crsjones/Southern-Cross-Computer-z80/SC-8x8_LED_Matrix/SC-8x8_R2/SC-8x8-R2.jpg

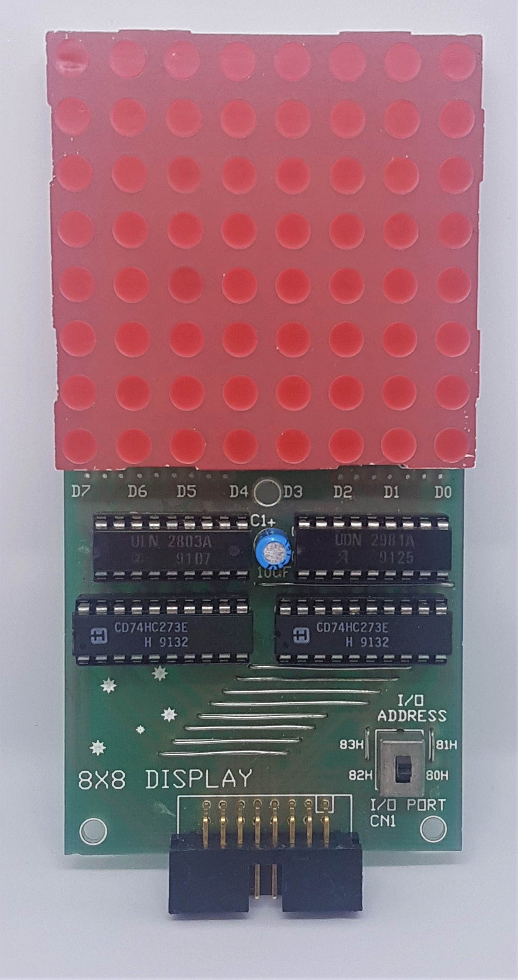
SC-8x8_LED_Matrix/SC-8x8_R2/SC-8x8-R2.jpg
