crsjones/Southern-Cross-Computer-z80/SC-8x8_LED_Matrix/SC-8x8_R4/Link.png

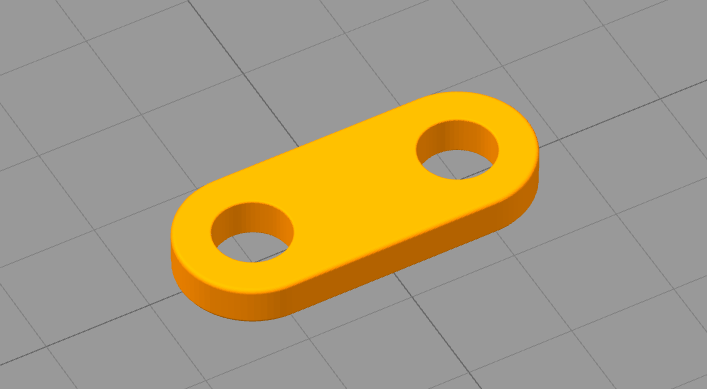
SC-8x8_LED_Matrix/SC-8x8_R4/Link.png
