crsjones/Southern-Cross-Computer-z80/SC-6850_Serial/SC-Serial_R1/SC-Serial_R1_PCB.jpg

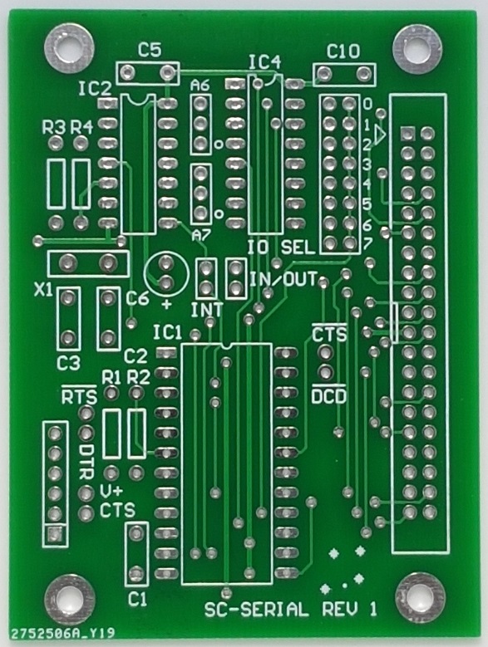
SC-6850_Serial/SC-Serial_R1/SC-Serial_R1_PCB.jpg
