crsjones/Southern-Cross-Computer-z80/SC-6850_Serial/SC-Serial_R2/SC-Serial_R2_PCB.jpg

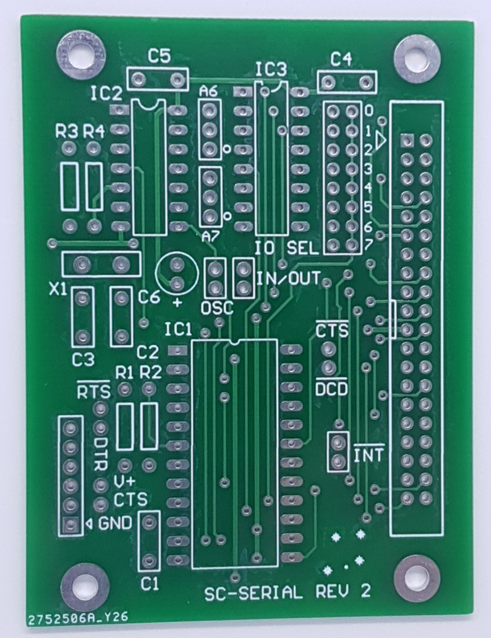
SC-6850_Serial/SC-Serial_R2/SC-Serial_R2_PCB.jpg
