crsjones/Southern-Cross-Computer-z80/SC-ALED/ALED10.png

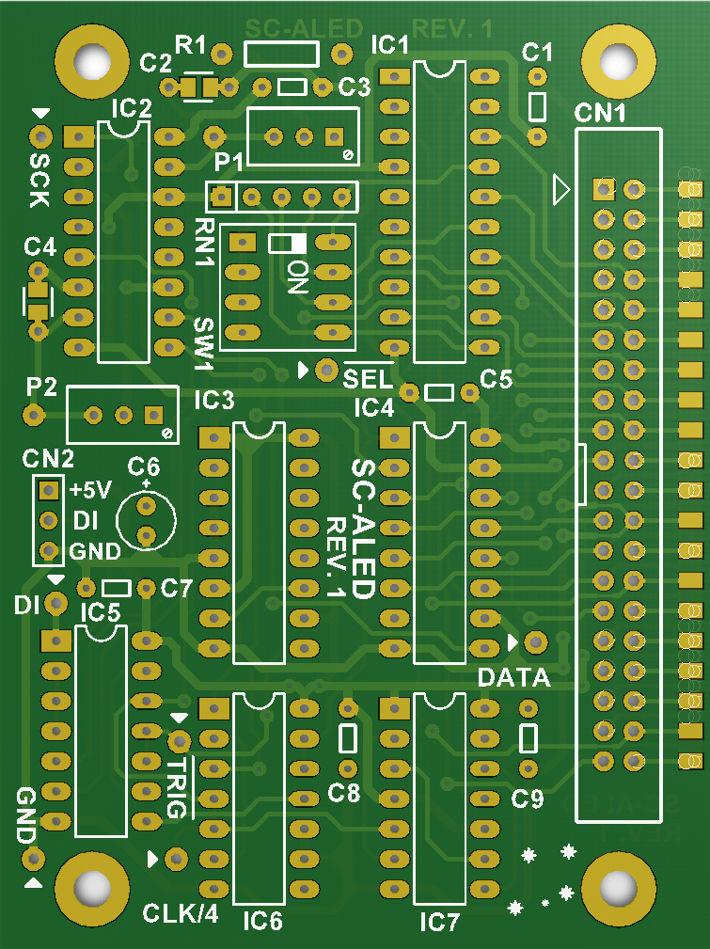
SC-ALED/ALED10.png
