crsjones/Southern-Cross-Computer-z80/SC-APU/SC-APU-R1/SC-APU-R1_PCB.jpg

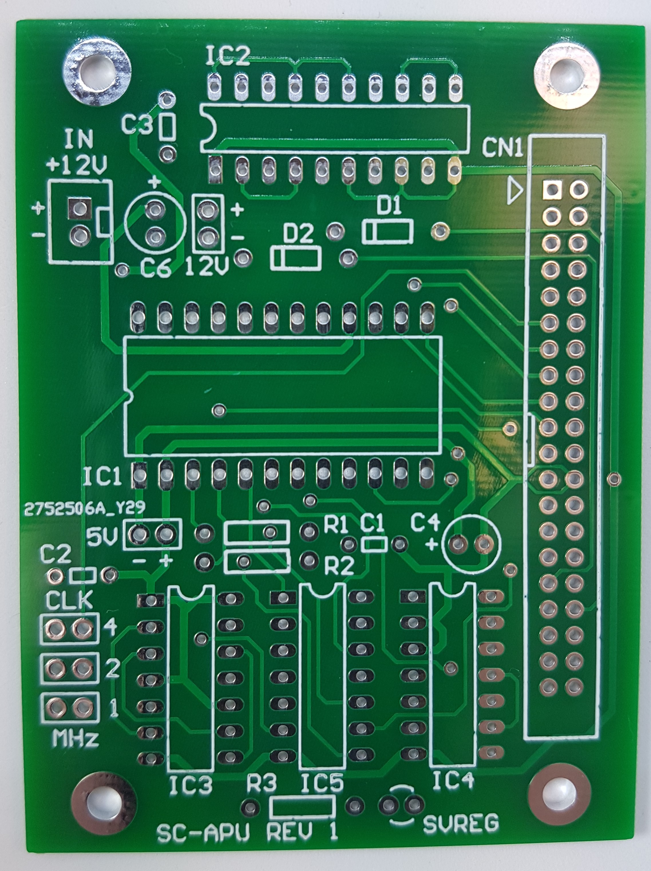
SC-APU/SC-APU-R1/SC-APU-R1_PCB.jpg
