crsjones/Southern-Cross-Computer-z80/SC-CF/SC-CFA-01_PCA.jpg

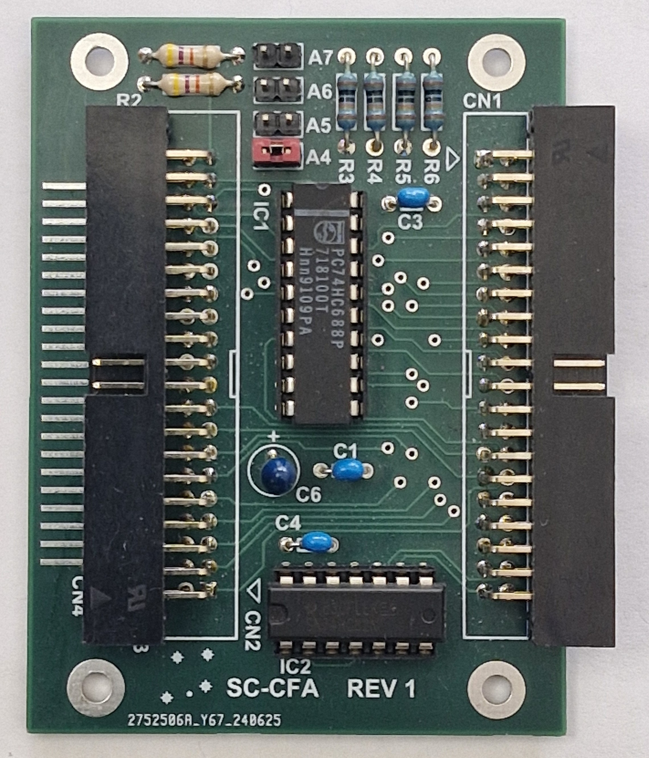
SC-CF/SC-CFA-01_PCA.jpg
