crsjones/Southern-Cross-Computer-z80/SC-CF/SC-CFA-02-PCB.png

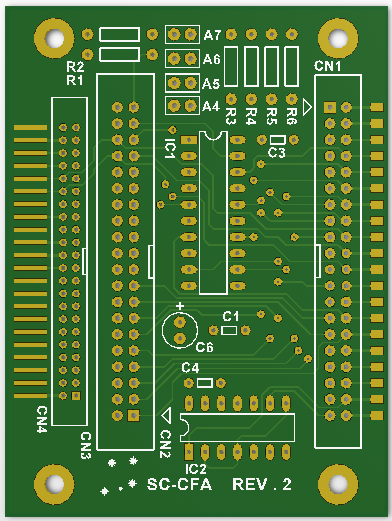
SC-CF/SC-CFA-02-PCB.png
