crsjones/Southern-Cross-Computer-z80/SC-CF/SC-CFA-FULL.jpg

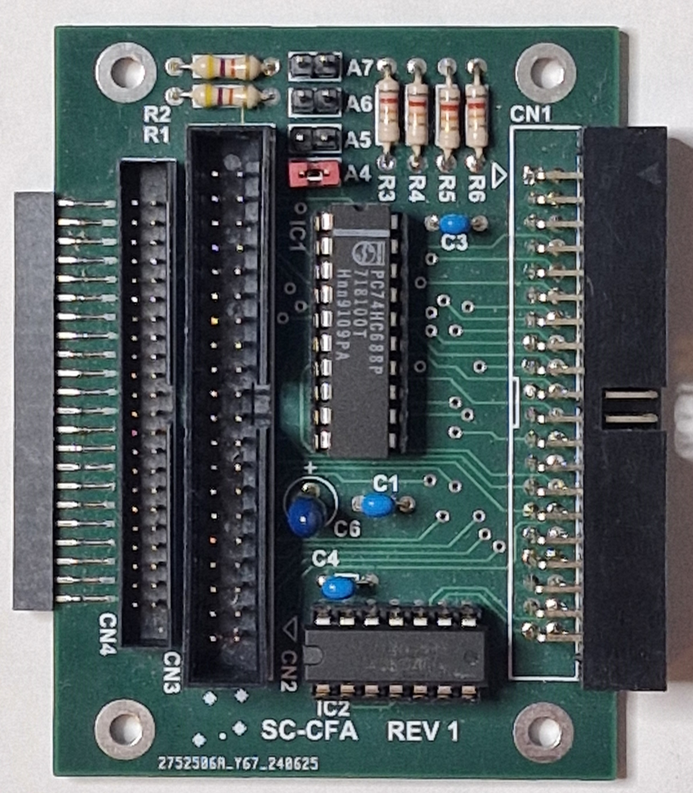
SC-CF/SC-CFA-FULL.jpg
