crsjones/Southern-Cross-Computer-z80/SC-CPU/Discrete Oscillator.jpg

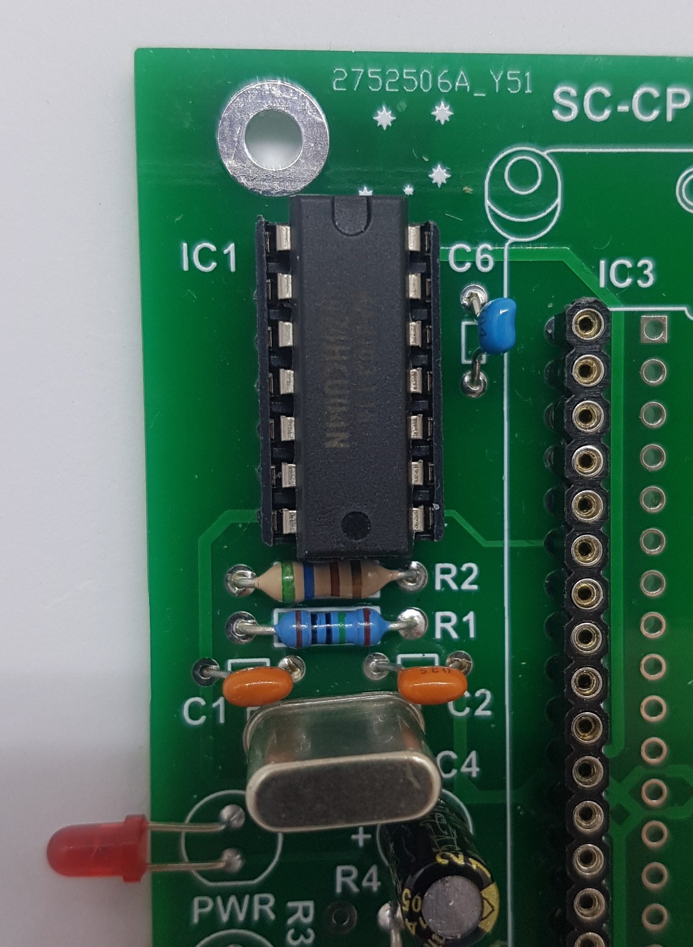
SC-CPU/Discrete Oscillator.jpg
