crsjones/Southern-Cross-Computer-z80/SC-CPU/SC-CPU-Blank.jpg

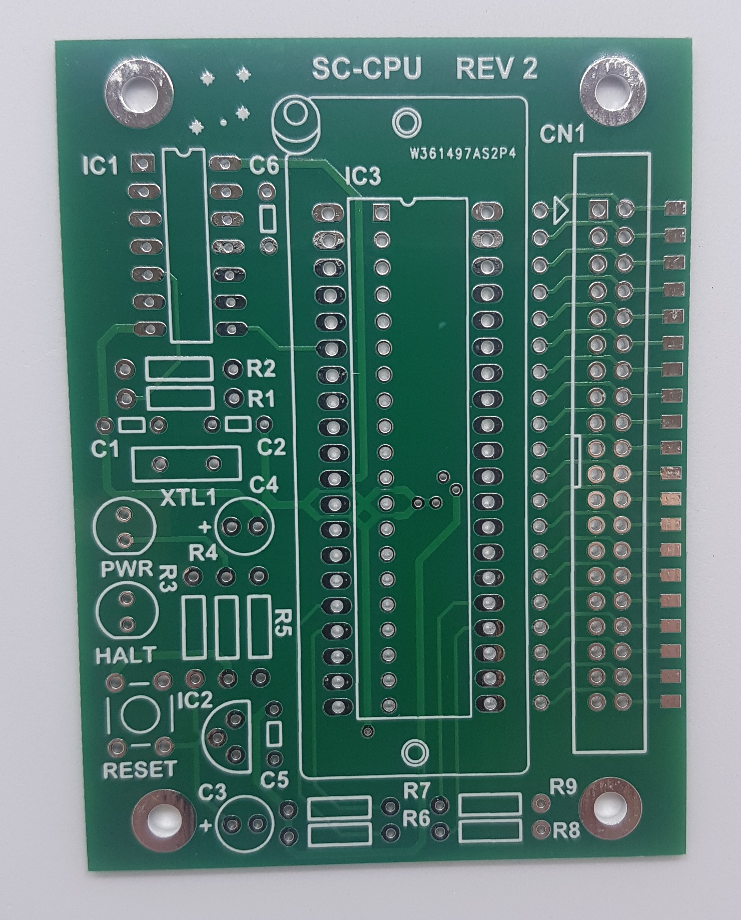
SC-CPU/SC-CPU-Blank.jpg
