crsjones/Southern-Cross-Computer-z80/SC-GBCART/SC-GBCART_R1.jpg

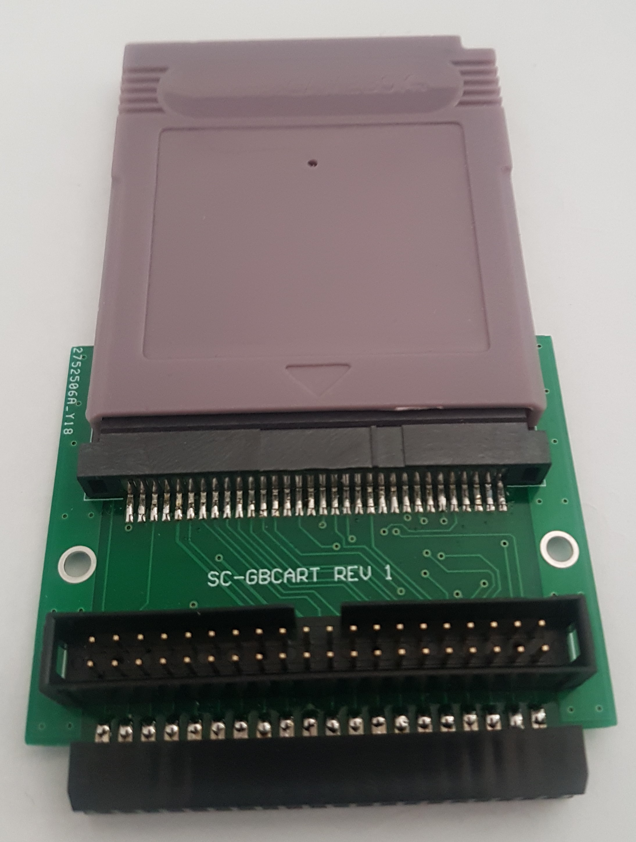
SC-GBCART/SC-GBCART_R1.jpg
