crsjones/Southern-Cross-Computer-z80/SouthernCrossSBC_PCB_R2/SC_R2.jpg

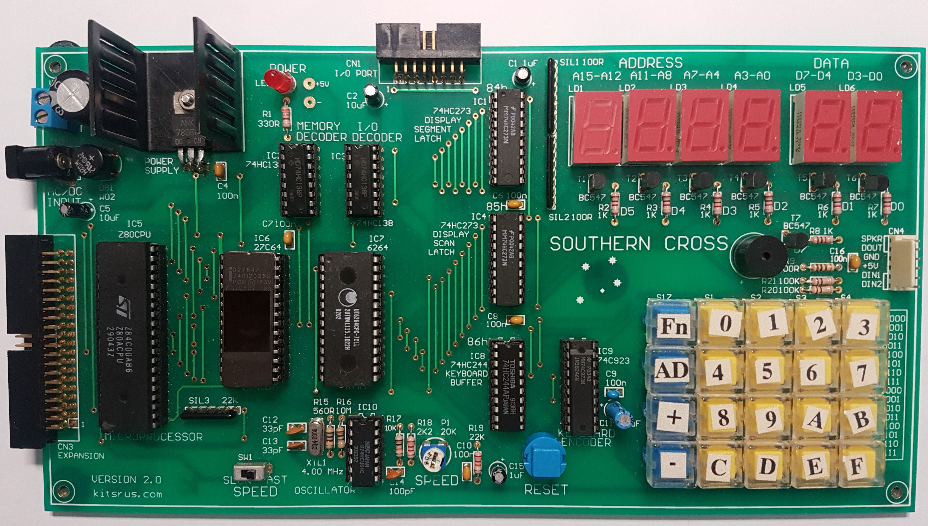
SouthernCrossSBC_PCB_R2/SC_R2.jpg
