crsjones/Southern-Cross-Computer-z80/SouthernCrossSBC_PCB_R3/SC30_Top.jpg

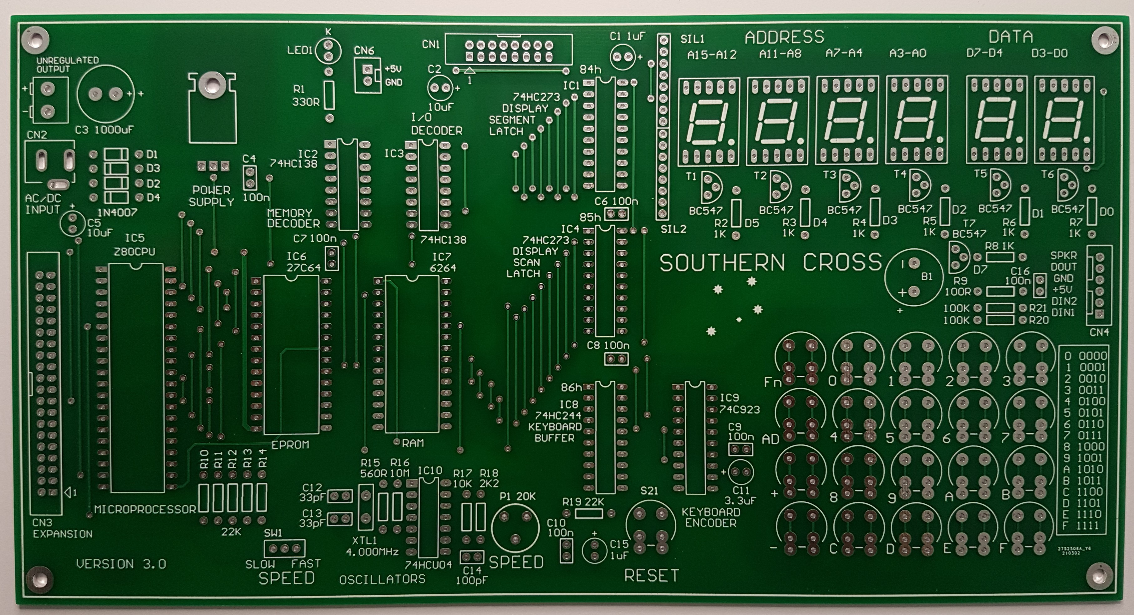
SouthernCrossSBC_PCB_R3/SC30_Top.jpg
