crsjones/Southern-Cross-Computer-z80/SouthernCrossSBC_PCB_R33/SC33-PCB-Bottom.jpg

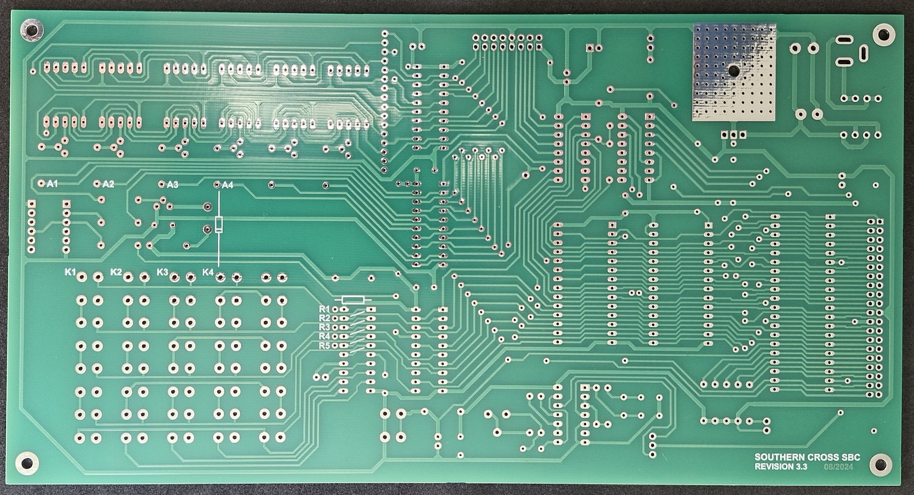
SouthernCrossSBC_PCB_R33/SC33-PCB-Bottom.jpg
