crsjones/Southern-Cross-Computer-z80/SouthernCrossSBC_PCB_R33/SC33-PCB-TOP.jpg

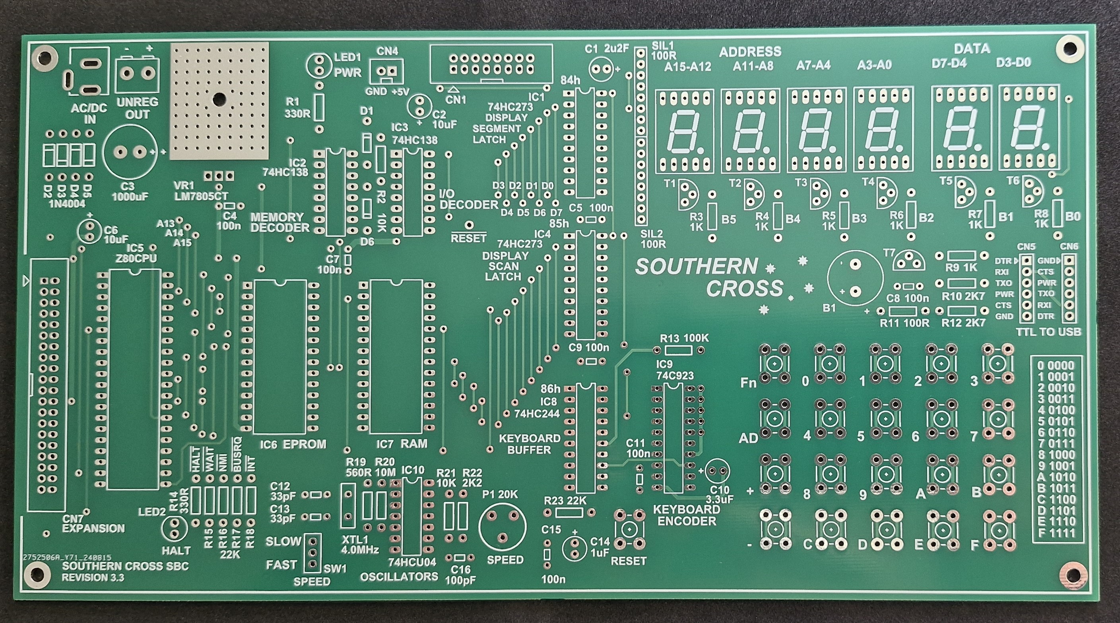
SouthernCrossSBC_PCB_R33/SC33-PCB-TOP.jpg
