crsjones/Southern-Cross-Computer-z80/SC-BP_Backplane/SC-BP-02/SC-BP-01ComponentOverlayandBOM.pdf

## SC-BP Expansion Backplane Rev. 1

## Component Overlay

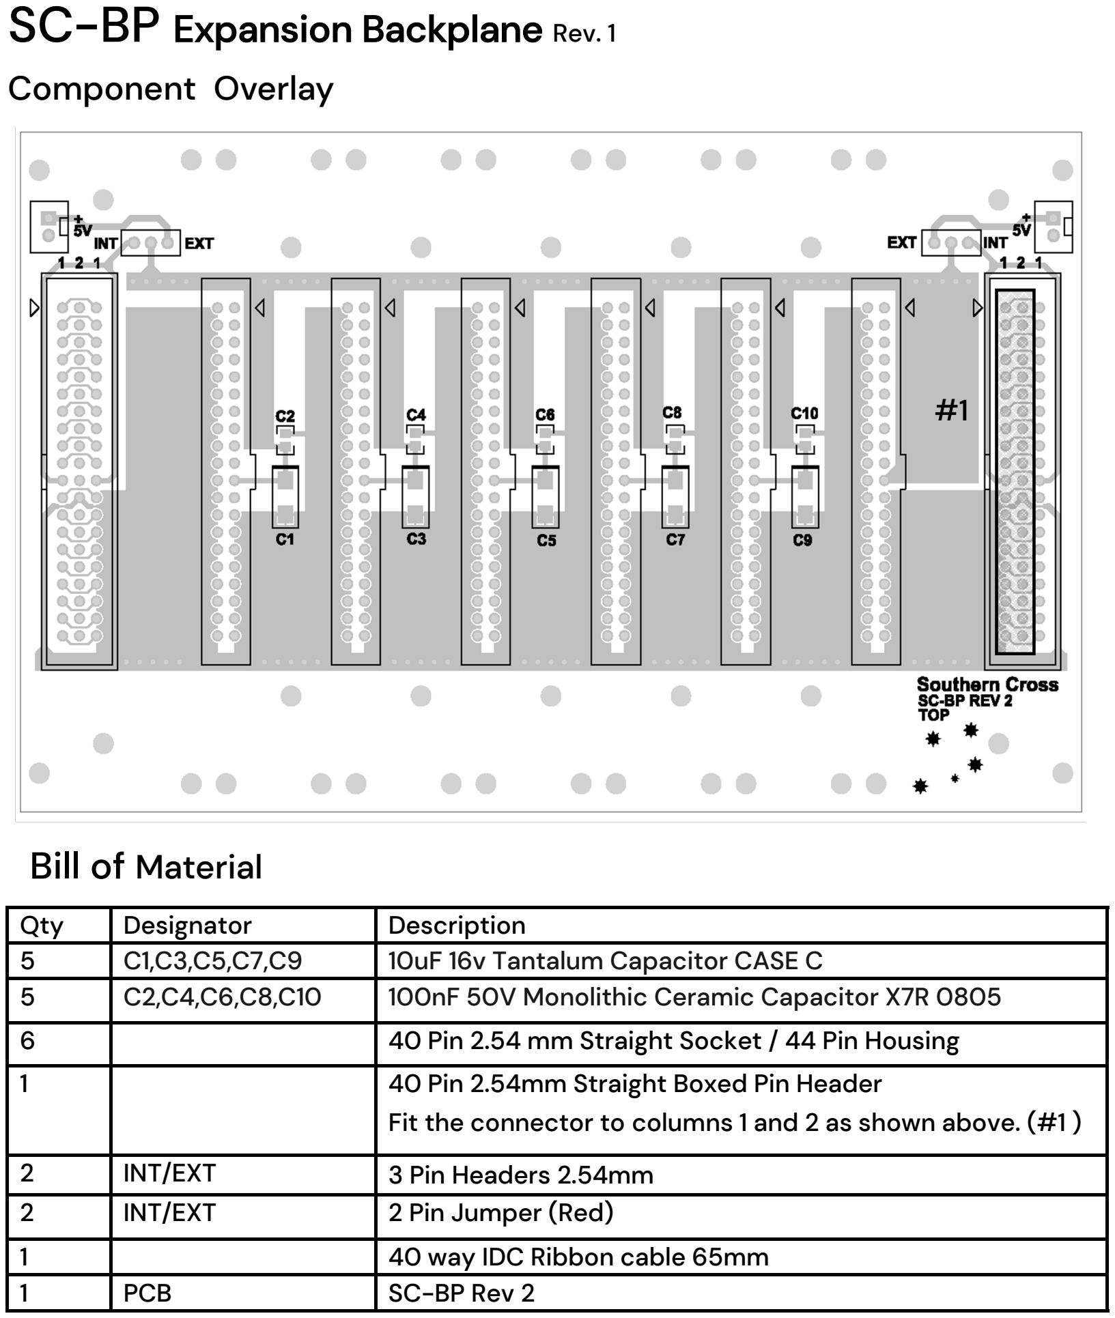
[picture p46: page 1]

## Bill of Material

Qty | Designator | Description
5 | C1,C3,C5,C7,C9 | 10uF 16v Tantalum Capacitor CASE C
5 | C2,C4,C6,C8,C10 | 100nF 50V Monolithic Ceramic Capacitor X7R 0805
6 40 Pin 2.54 mm Straight Socket / 44 Pin Housing
1 40 Pin 2.54mm Straight Boxed Pin Header | | Fit the connector to columns 1 and 2 as shown above. (#1 )
2 | INT/EXT | 3 Pin Headers 2.54mm
2 | INT/EXT | 2 Pin Jumper (Red)
1 40 way IDC Ribbon cable 65mm
1 | PCB | SC-BP Rev 2

#1
