crsjones/Southern-Cross-Computer-z80/SC-APU/SC-APU-R1/SC-APU-R1_Assembled.jpg

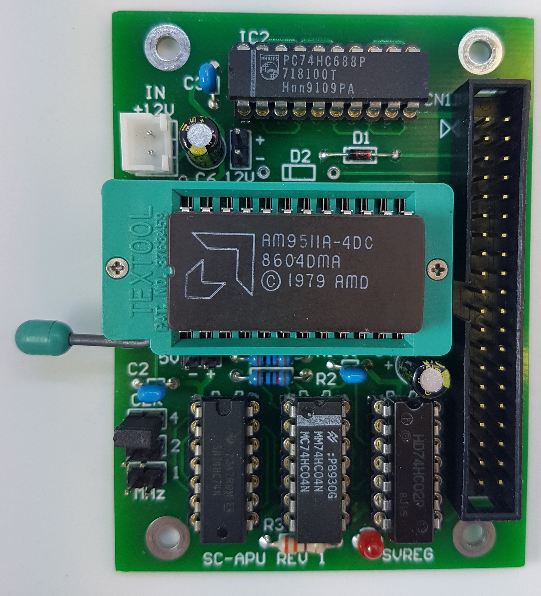
SC-APU/SC-APU-R1/SC-APU-R1_Assembled.jpg
