crsjones/Southern-Cross-Computer-z80/SC-APU/SC-APU-R2/SC-APU-R2_Assembled.jpg

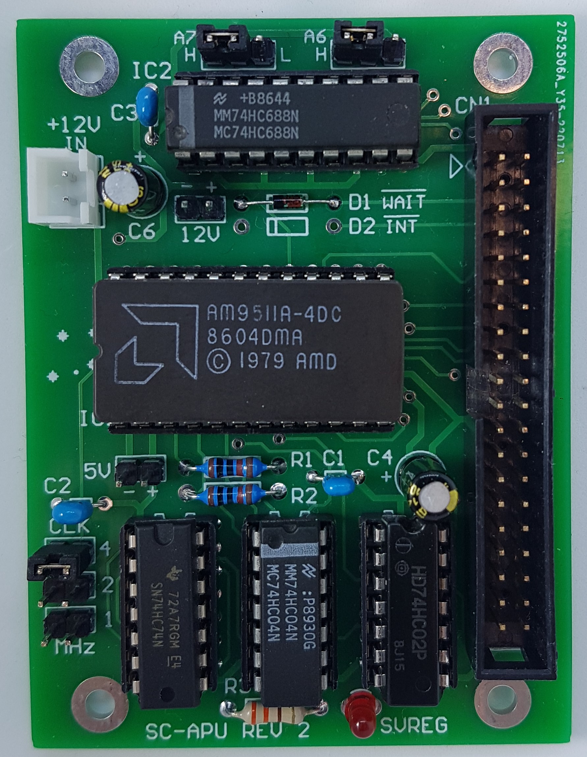
SC-APU/SC-APU-R2/SC-APU-R2_Assembled.jpg
