crsjones/Southern-Cross-Computer-z80/SC-CPU/SC-CPU-Assembled.jpg

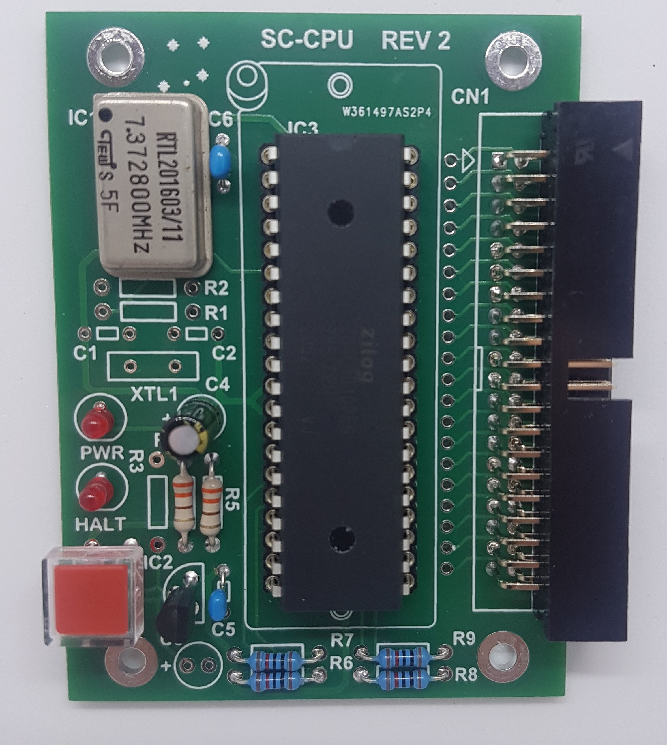
SC-CPU/SC-CPU-Assembled.jpg
