crsjones/Southern-Cross-Computer-z80/SC-MEM/SC-MEM-02-Assembled.jpg

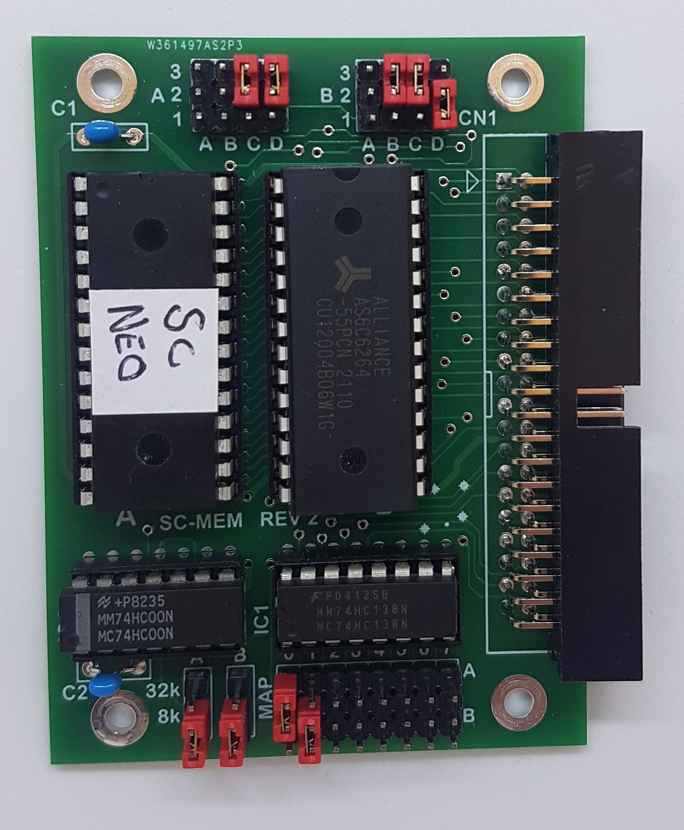
SC-MEM/SC-MEM-02-Assembled.jpg
