crsjones/Southern-Cross-Computer-z80/SouthernCrossSBC_PCB_R32/SC_R32-Assembled.jpg

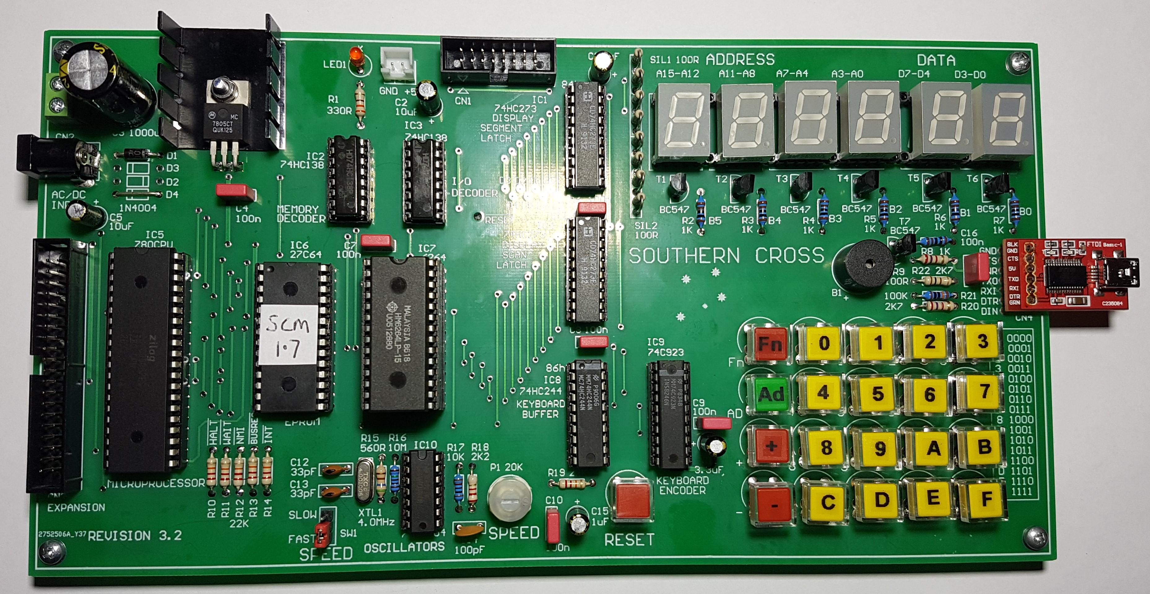
SouthernCrossSBC_PCB_R32/SC_R32-Assembled.jpg
