crsjones/Southern-Cross-Computer-z80/SC-8x8_LED_Matrix/SC-8x8_R4/SC-8X8_R5_Schematic.pdf

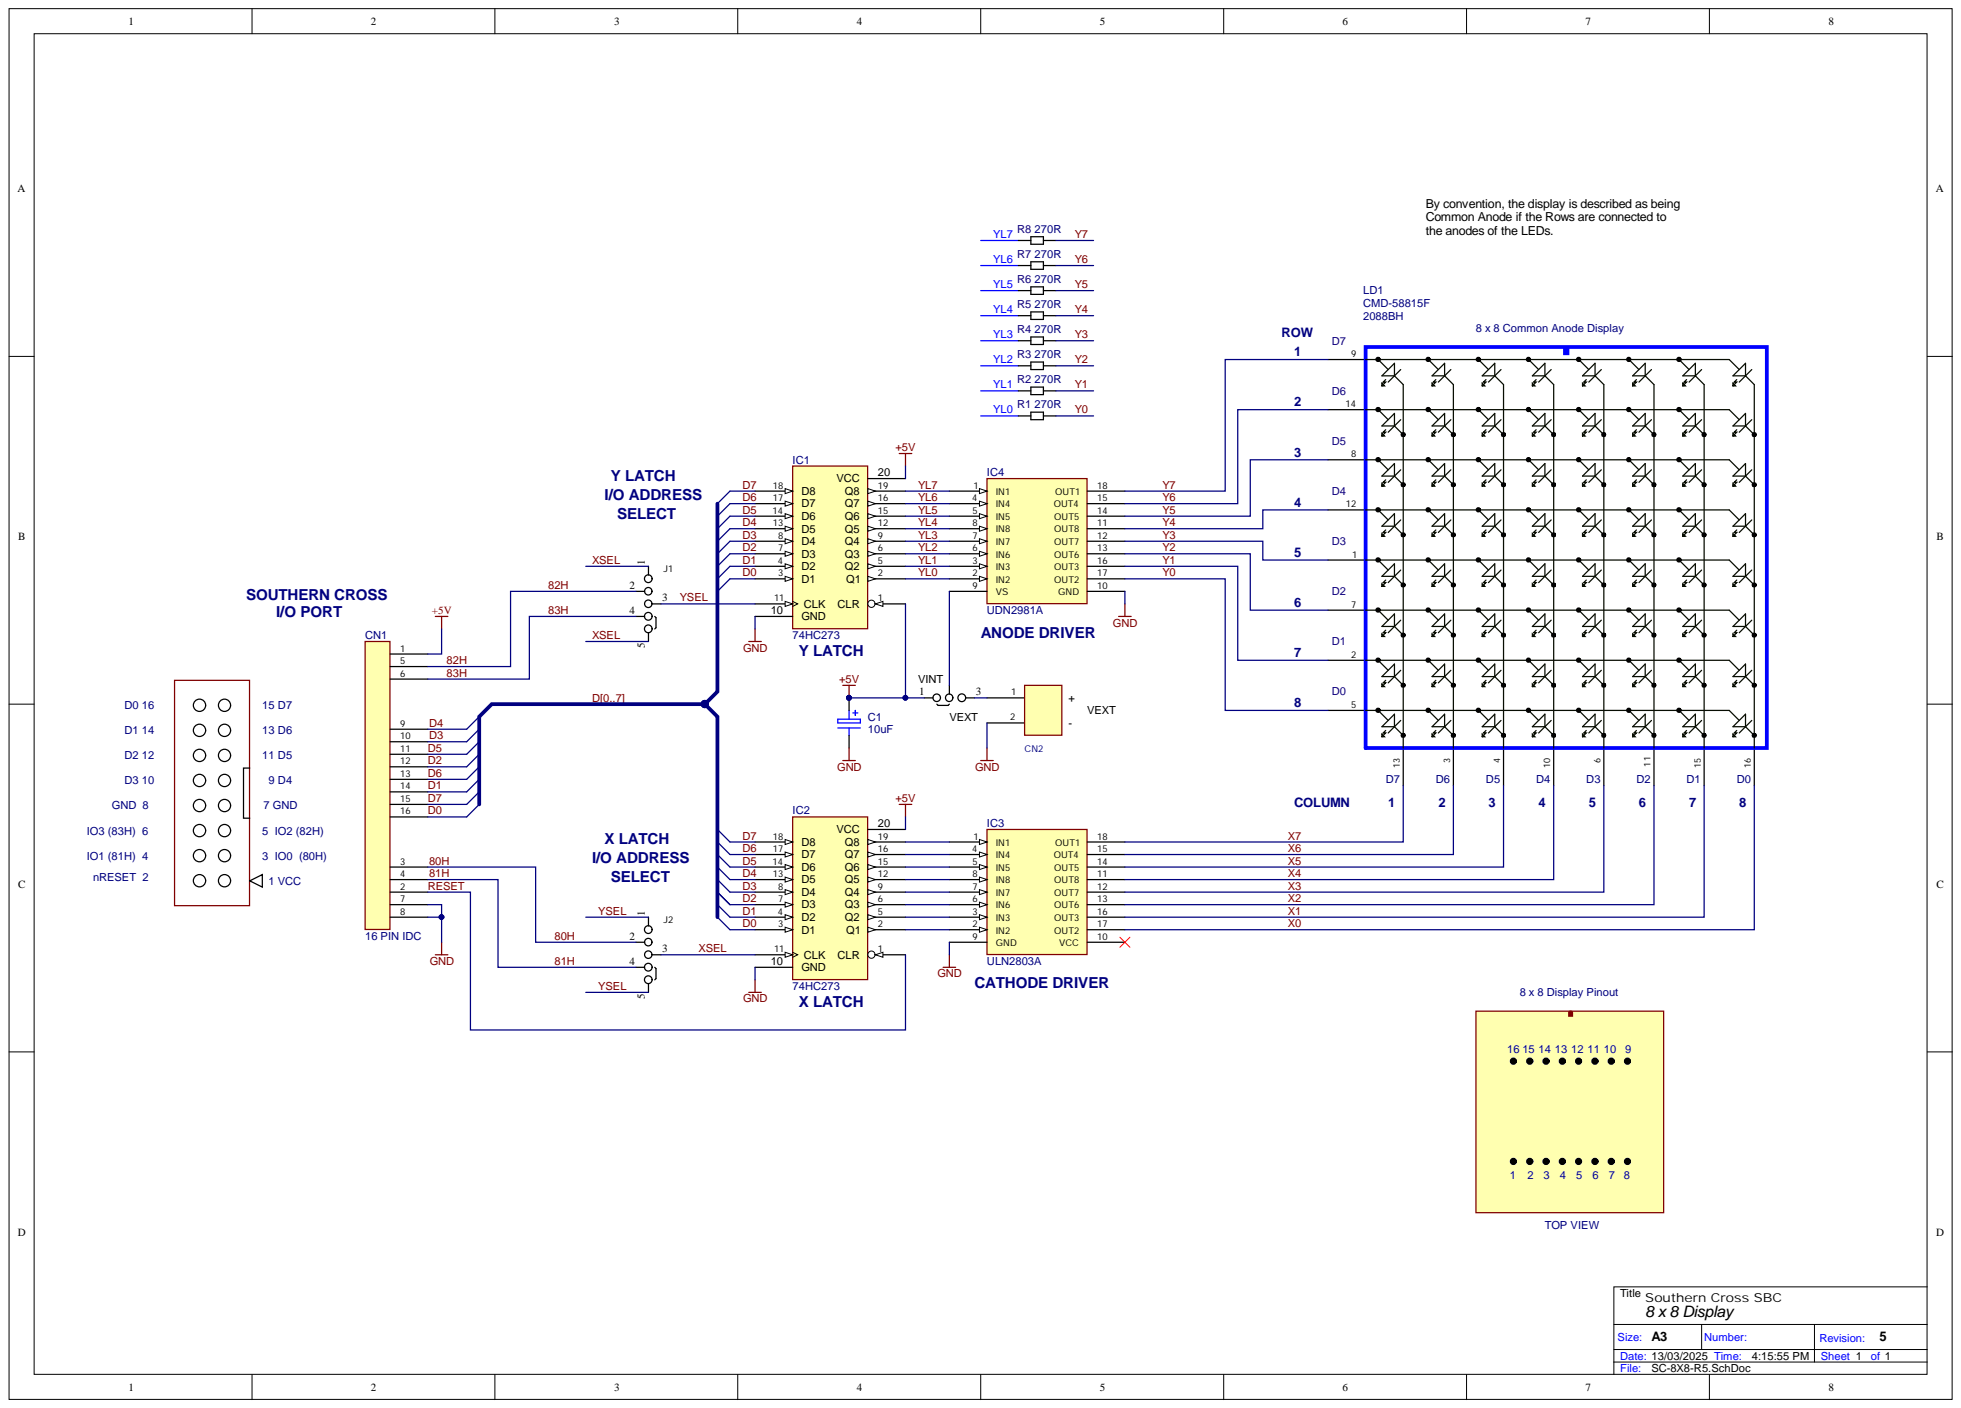
[picture p71: page 1]

8 | | Y 4
7 | Y 3
6 | | Y 2
3 | | Y 1

82H
83H

GND | 81H

Si ze: | Number: | Revis ion: 5
Date: 13/03/2025 T ime: 4:15:55 PM | | Sheet 1 of 1
