crsjones/Southern-Cross-Computer-z80/SC-8x8_LED_Matrix/SC-8x8_R3/SC-8X8-R3Schematic.pdf

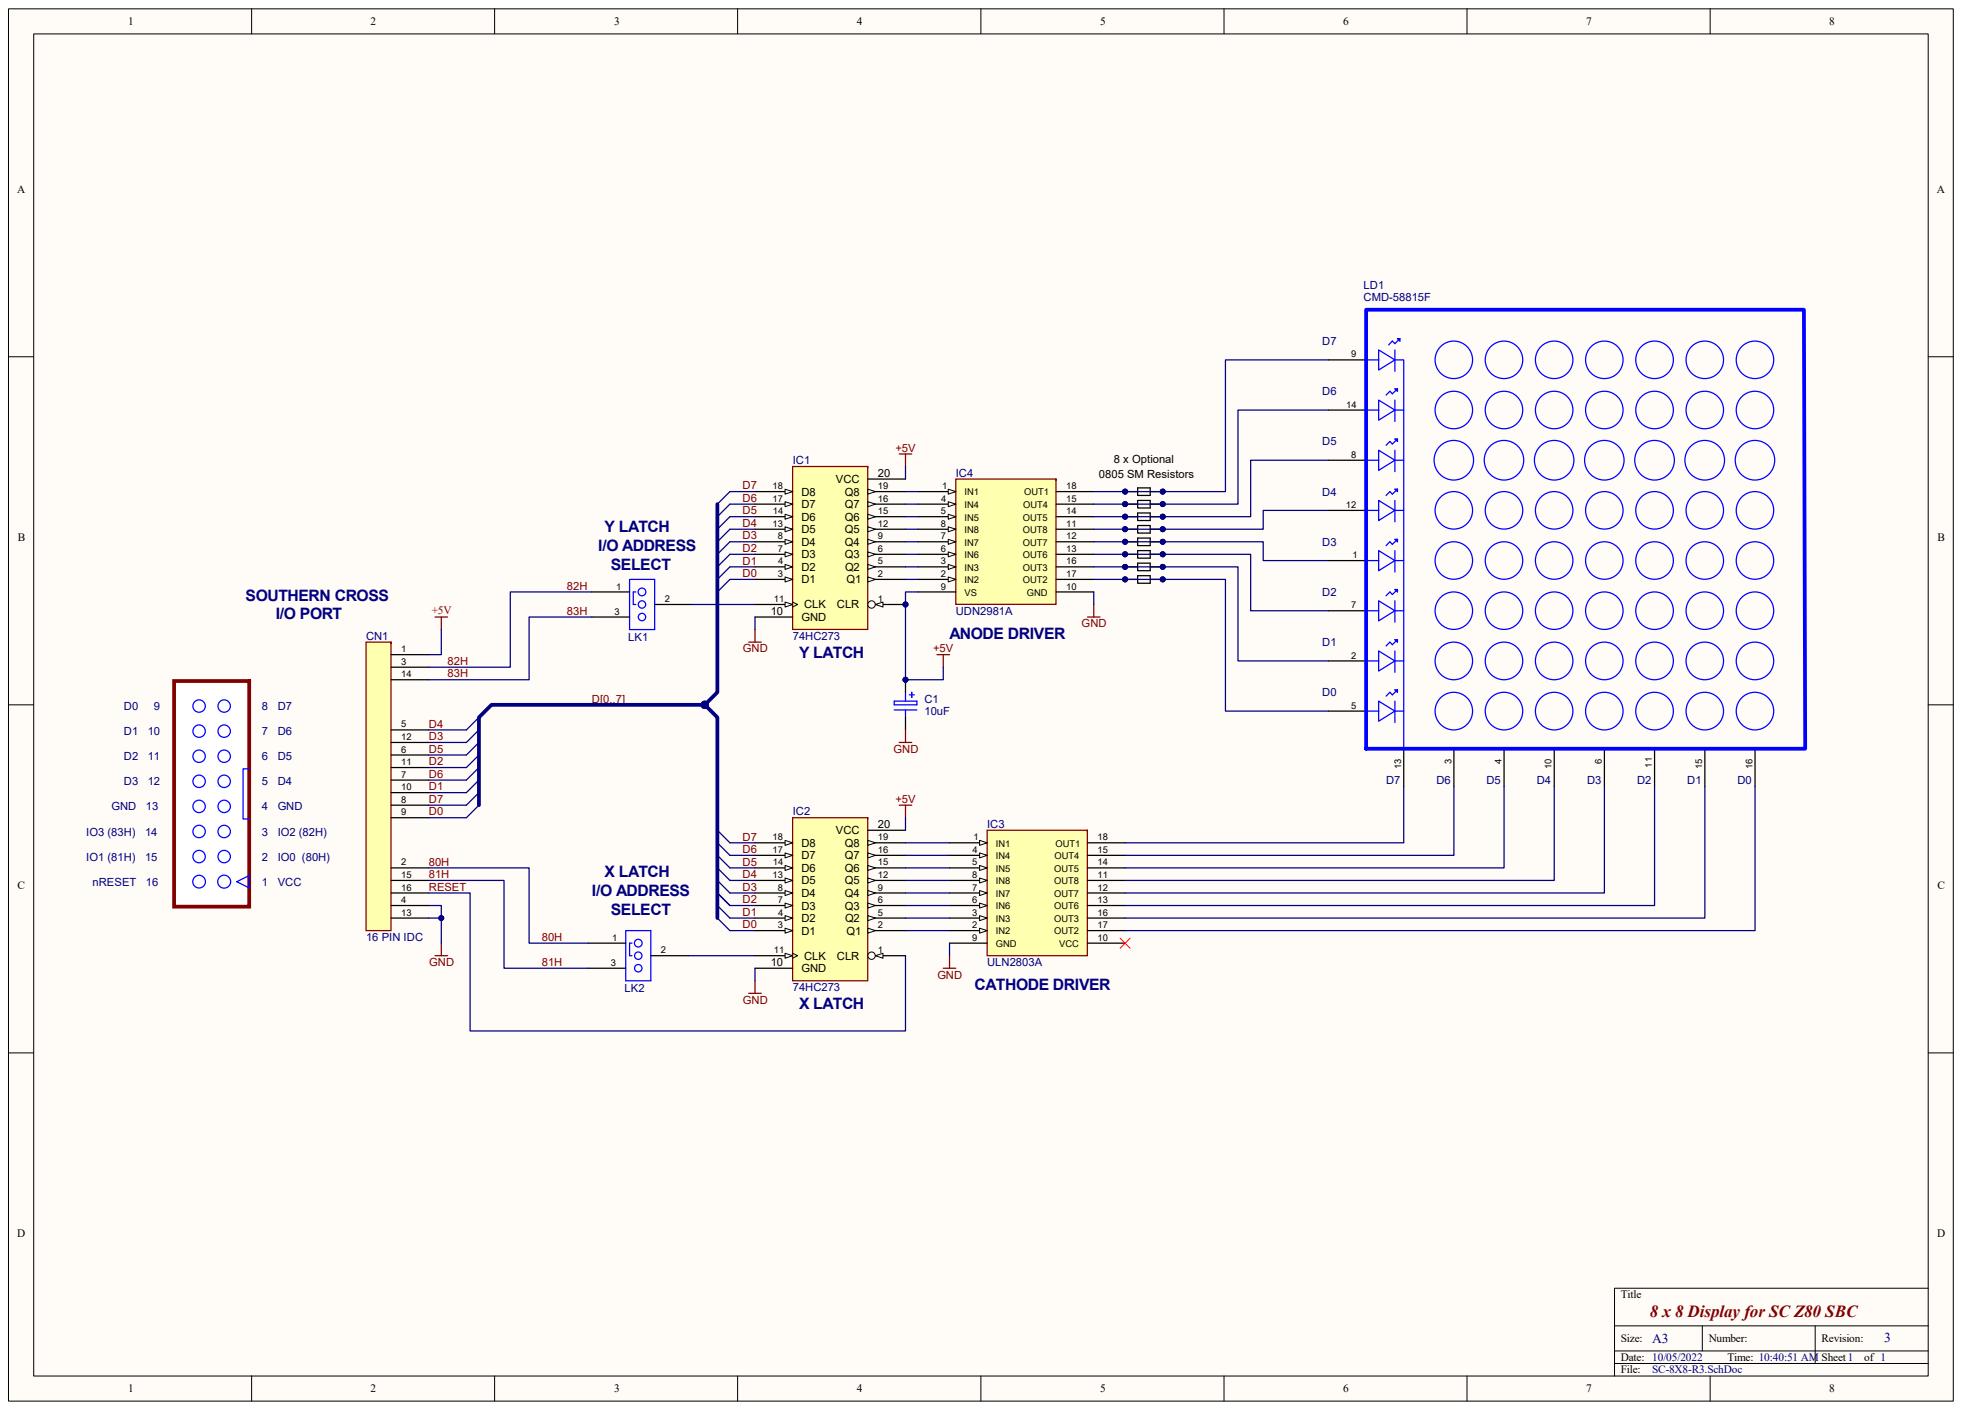
[picture p72: page 1]

GND 10
