crsjones/Southern-Cross-Computer-z80/SC-LATCH-LCD/SC-LCD1602.pdf

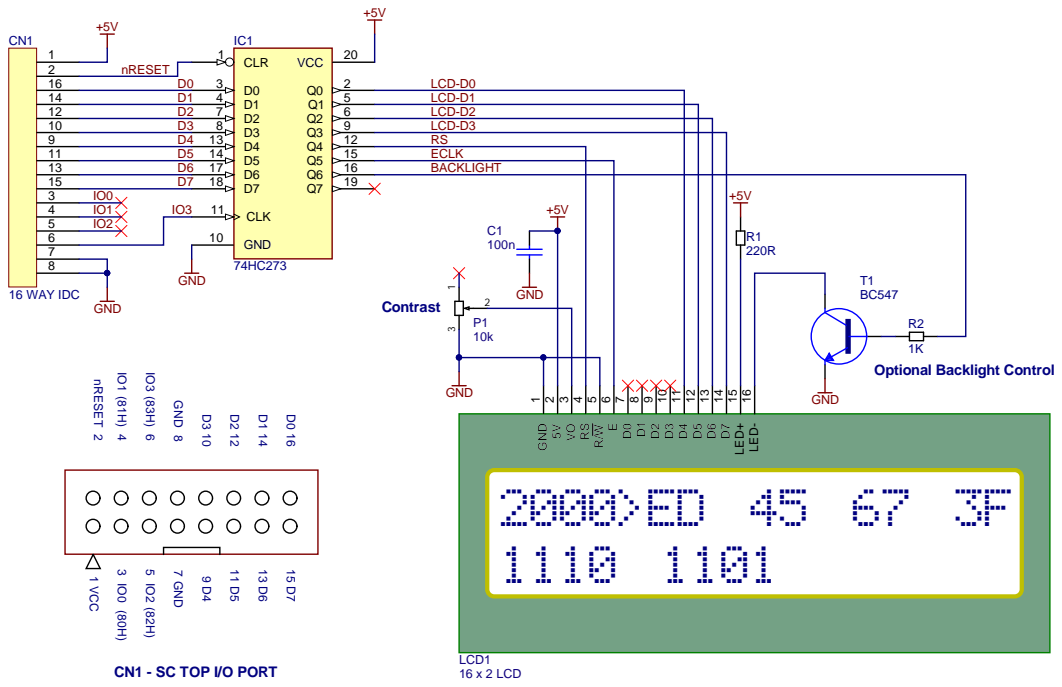
[picture p73: page 1]

5 6 | IO2 | GND 10

Size: A3 | Number: * | Revision: 1
Date: 20/04/2025 Time: 9:46:00 PM | | Sheet 1 of 1
