crsjones/Southern-Cross-Computer-z80/Docs/SC_KeyboardDisplaySS_34.pdf

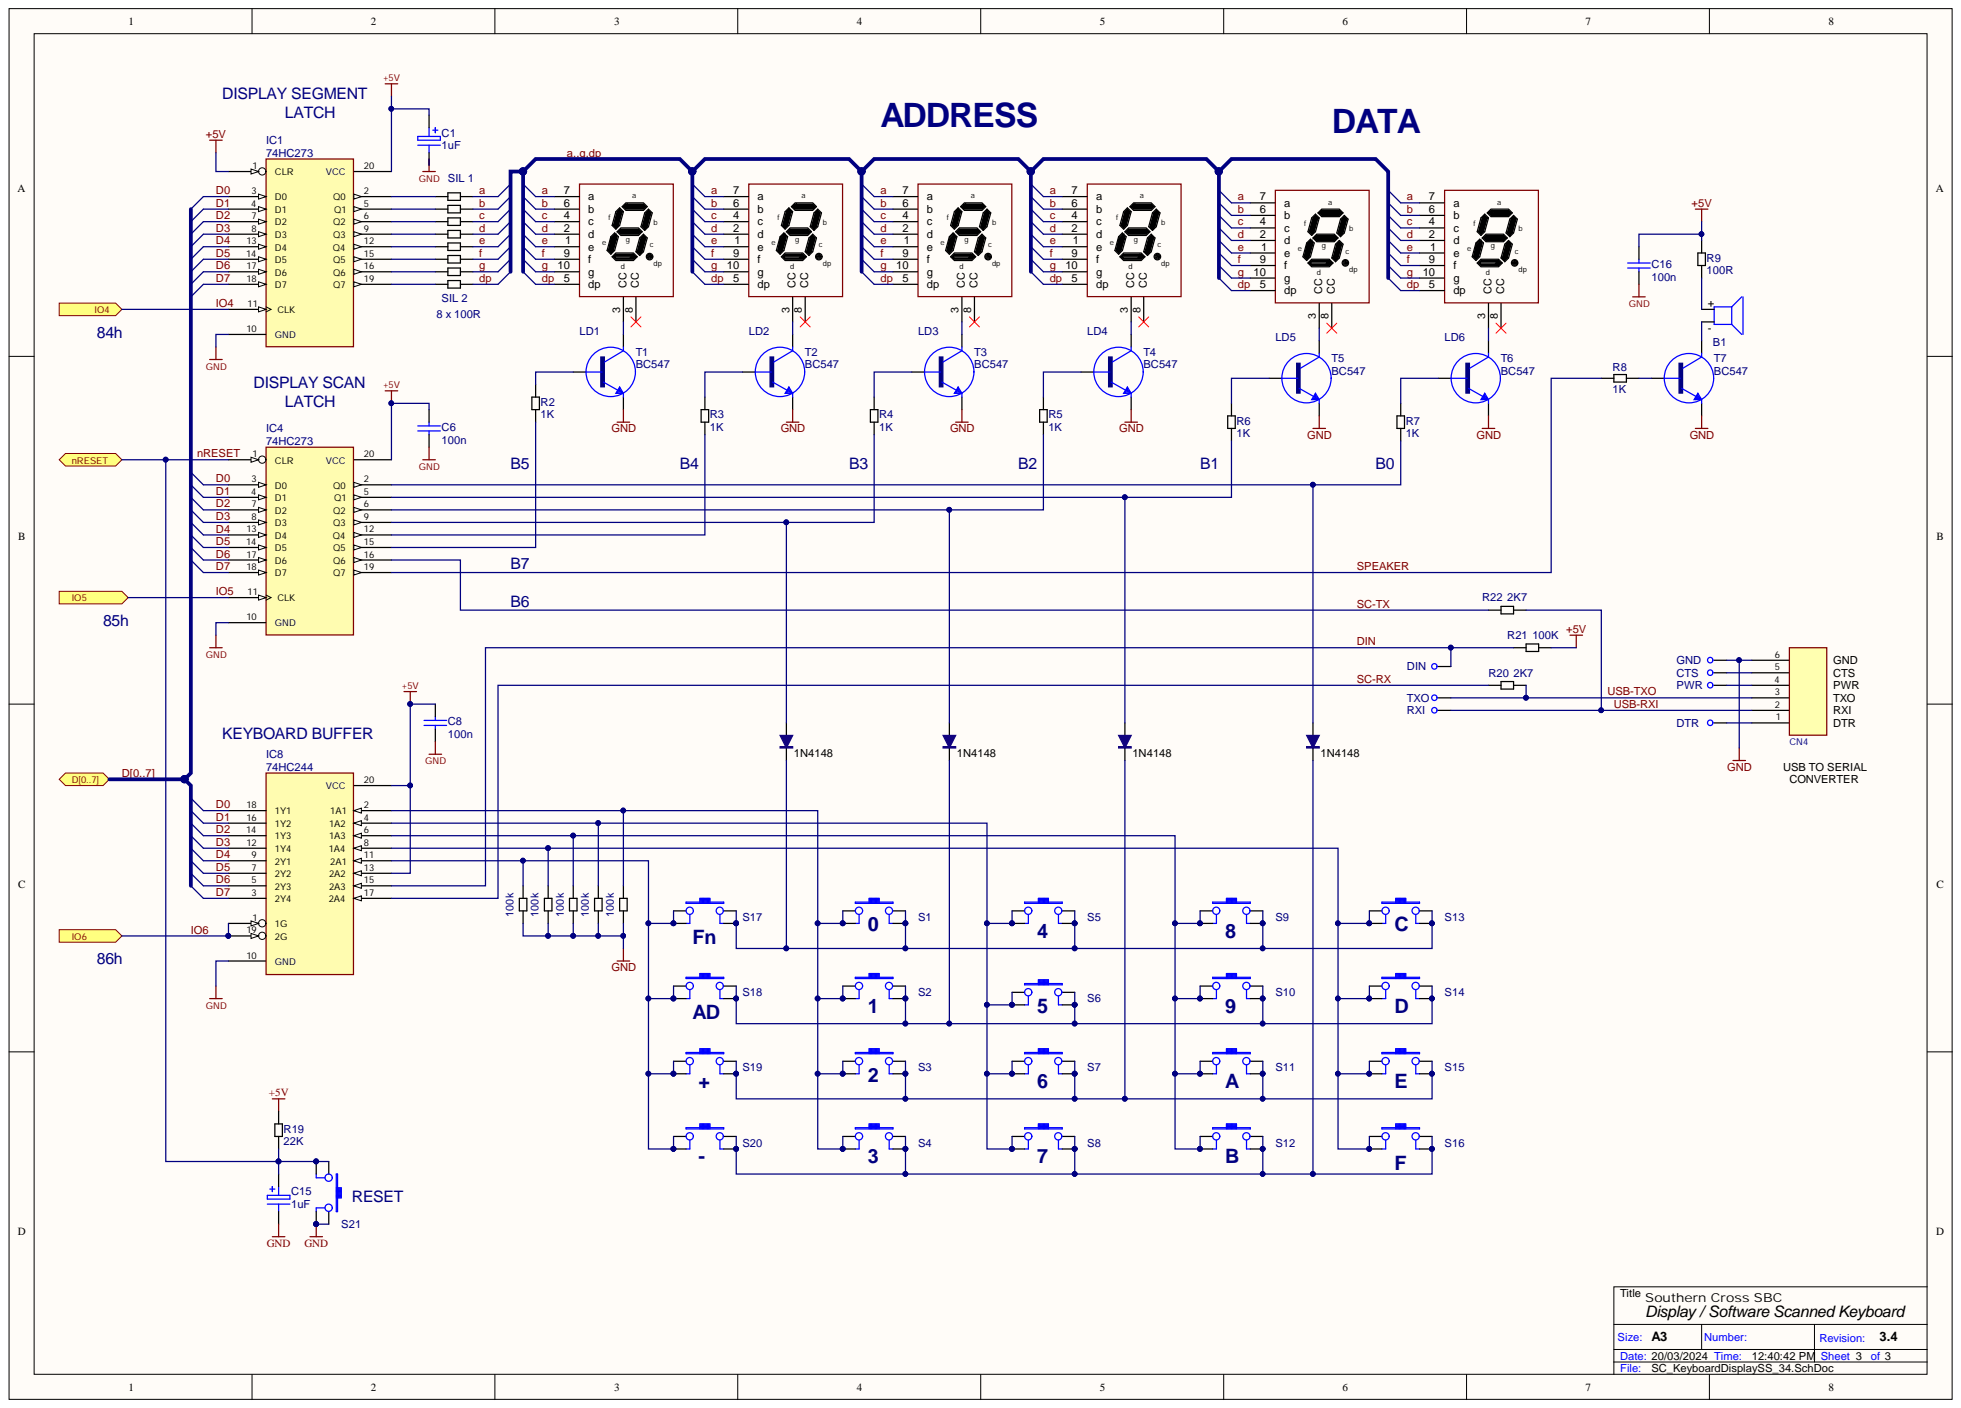
[picture p74: page 1]

CLR 1

B7 | | | SPEAKER

DIN | +5V

Title
Southern Cross SBC
Display / Software Scanned Keyboard

Size: A3 | Number: | Revision: 3.4
Date: 20/03/2024 Time: 12:40:42 PM | | Sheet 3 of 3
