crsjones/Southern-Cross-Computer-z80/Docs/MemoryDevices03.pdf

# 28 Pin EPROM, EEPROM and RAM Pinouts

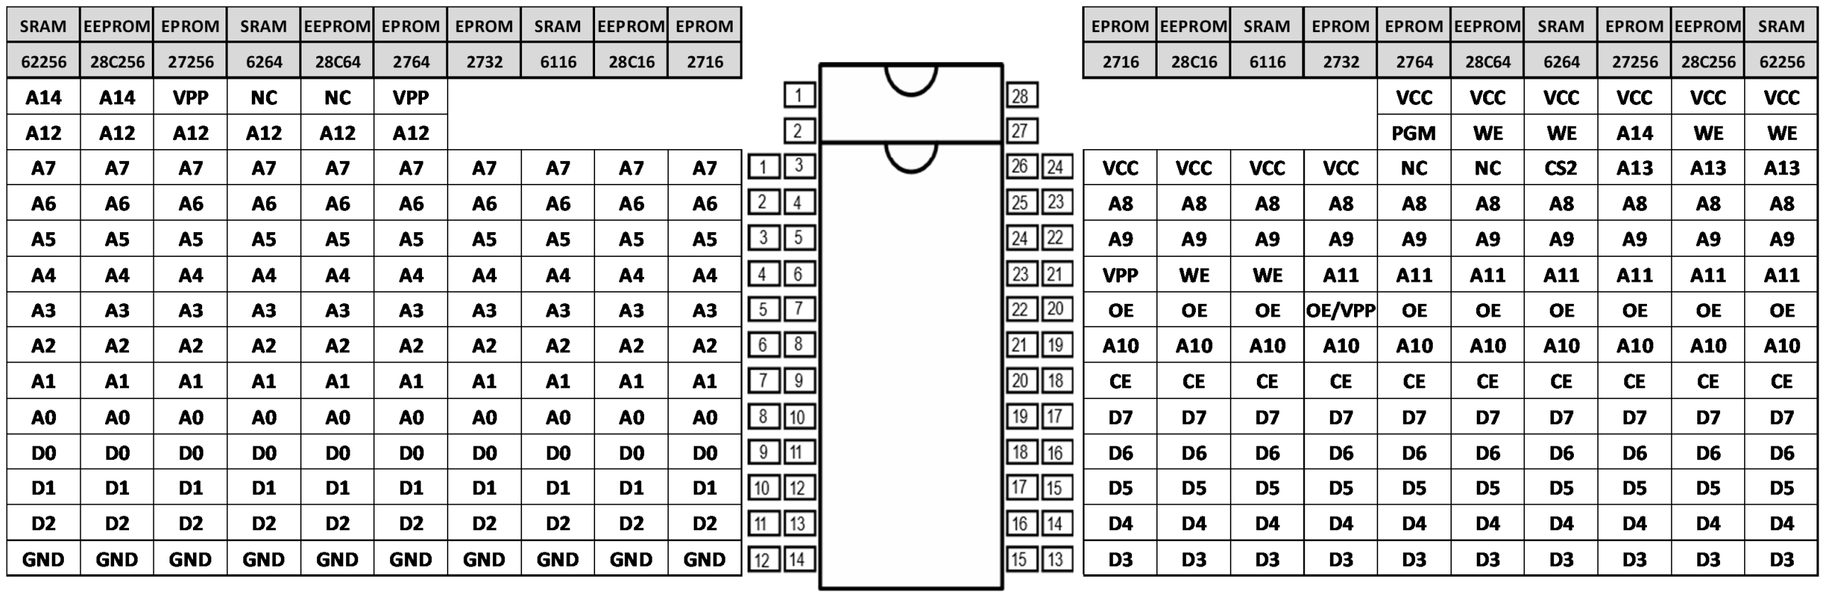
[picture p78: figure]

Note:
1. CE,OE,WE are Active low inputs.
2. VPP and PGM pins should be connected to VCC when not used in programming, except for the 2732 dual function pin 20, OE/VPP.

# Static RAM Pinouts

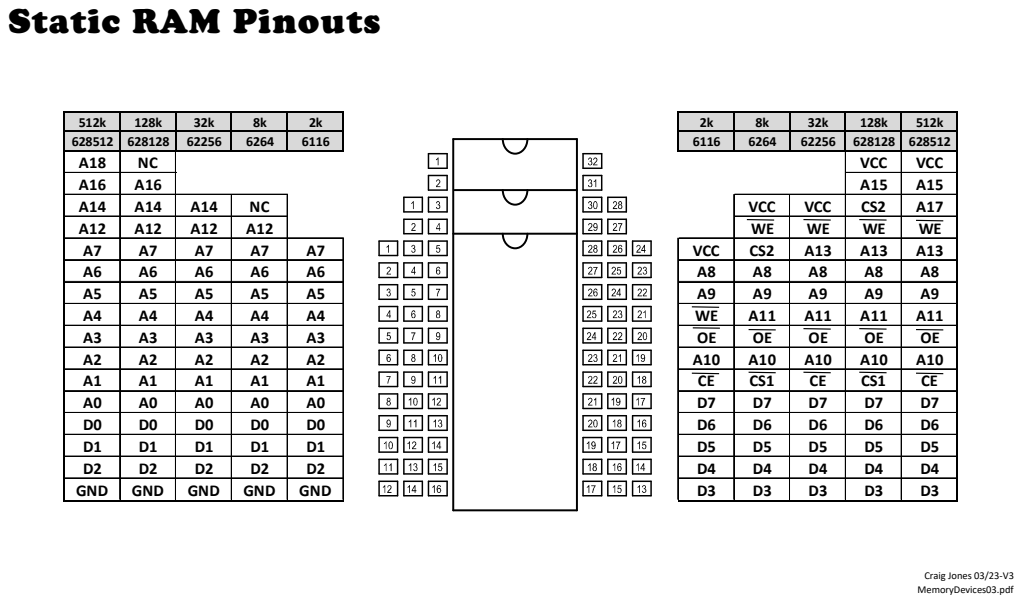
[picture p79: page 2]
