crsjones/Southern-Cross-Computer-z80/Docs/SC56KRamMod.pdf

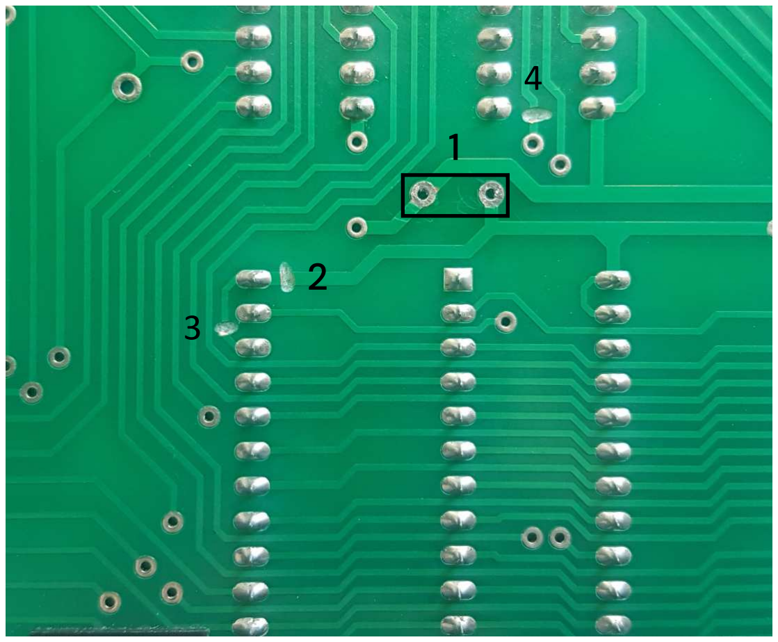
[picture p80: figure]

1. Remove C7.
2. Cut the track between Pin 28 IC7 (6264) and +5V.
3. Cut the track between Pin 26 IC7 (6264) and Pin 28 IC7 (6264).
4. Cut the track between Pin 20 IC7 (6264) and Pin 14 IC2 (74HC138).

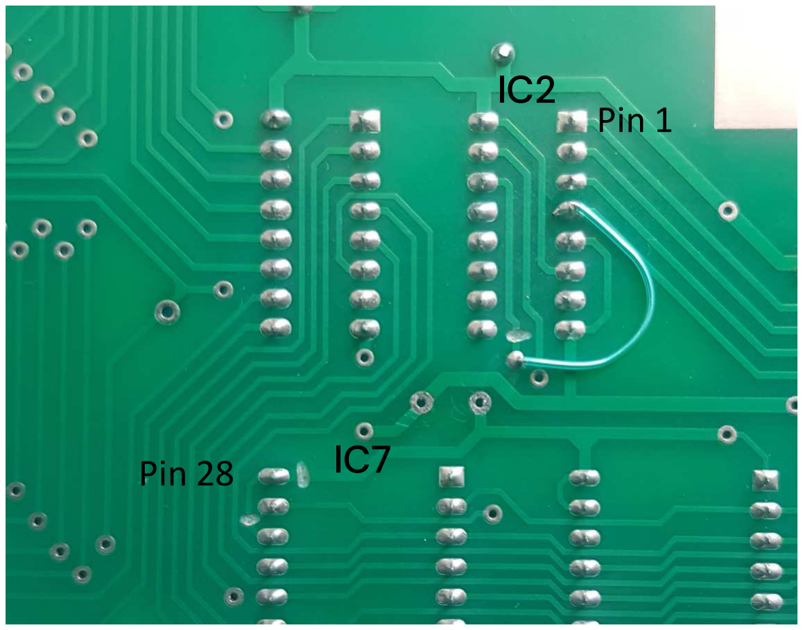
[picture p81: figure]
Pin 1; Pin 28

# 5. Connect Pin 20 IC7 (6264) to nMREQ Pin 4

IC2 (74HC138).

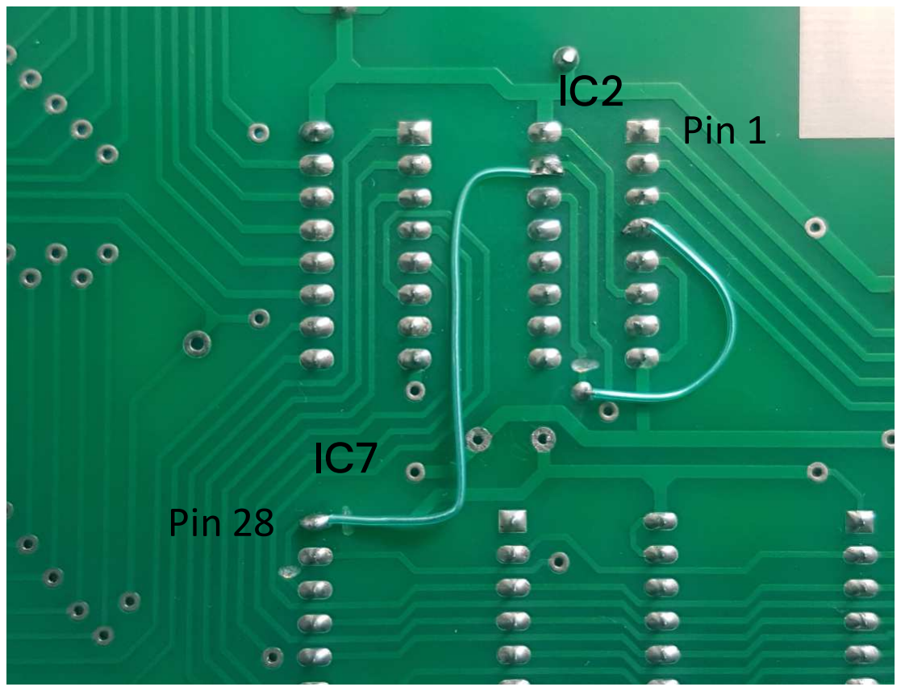
[picture p82: figure]
Pin 1; Pin 28

# 6. Connect Pin 28 IC7 (6264) to Pin 15 IC2

(74HC138).

# 56K RAM upgrade for the Southern Cross SBC

# Page 1

# You will need a 32 pin IC socket , a 128K x 8 Static Ram (SRAM) and some thin solid

core wire like wire wrap wire.

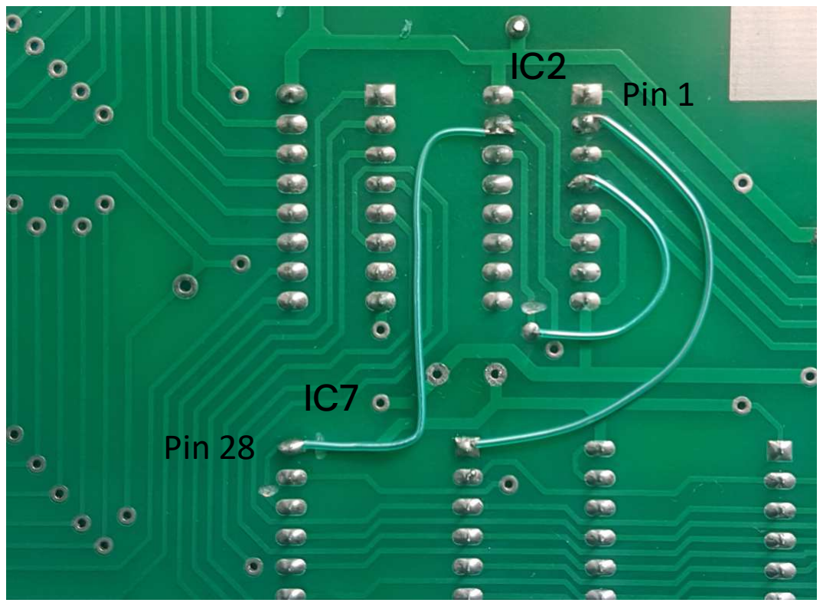
[picture p83: figure]
Pin 1; Pin 28

# 7. Connect Pin 1 IC7 (6264) to A14 Pin 2 IC2

(74HC138).

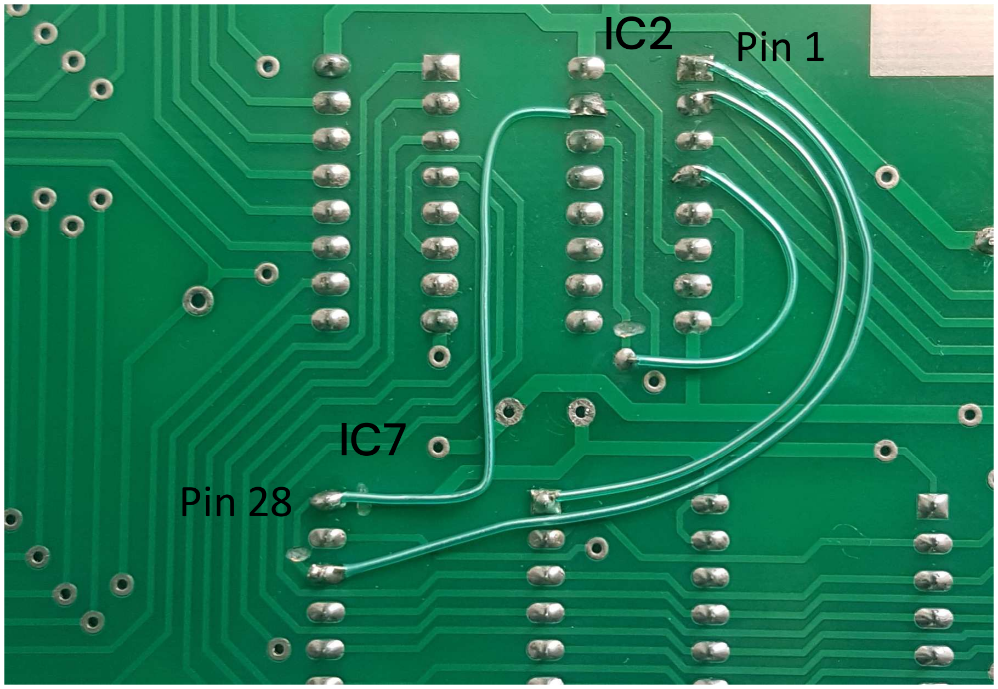
[picture p84: figure]
Pin 1; Pin 28

# 8. Connect Pin 26 IC7 (6264) to A13 Pin 1 IC2

(74HC138).

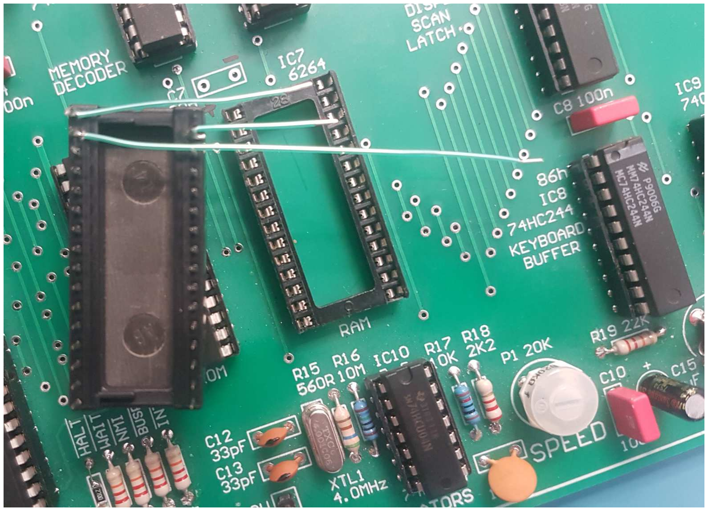
[picture p85: figure]

# 9. Put a 128k x 8 SRAM (like HM628128) in a

# 32 Pin IC socket to dissipate the heat from soldering to stop the socket plastic from

melting.

# 10. Solder short wires on Pins 2 and 32 and a

5 to 6 cm wire on Pin 31.

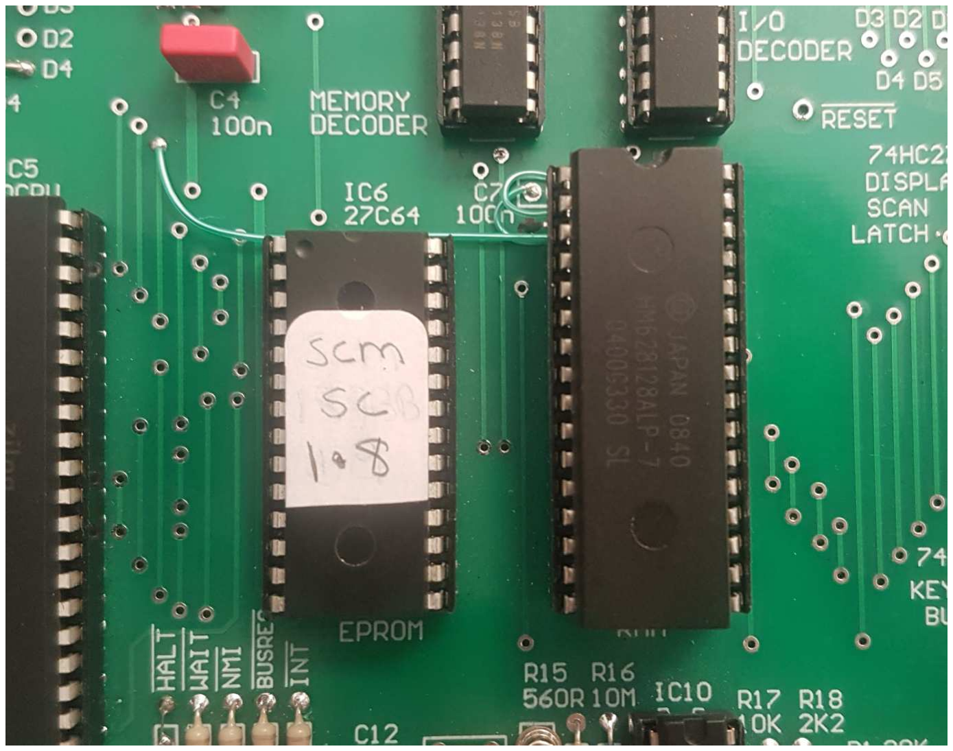
[picture p86: figure]

# 11. Connect the wire from Pin 2 to GND, the right

pad of the removed C7.

# 12. Connect the wire from Pin 32 to +5V the left side

of the removed C7.

# 13. Connect the wire from Pin 31 to A15, the bottom

via of the three diagonal vias to the left of C4.

# 14. Solder a 100nF Ceramic capacitor on the back of

the board in the C7 position.

# 56K RAM upgrade for the Southern Cross SBC

# Page 2

## V C C

1 6

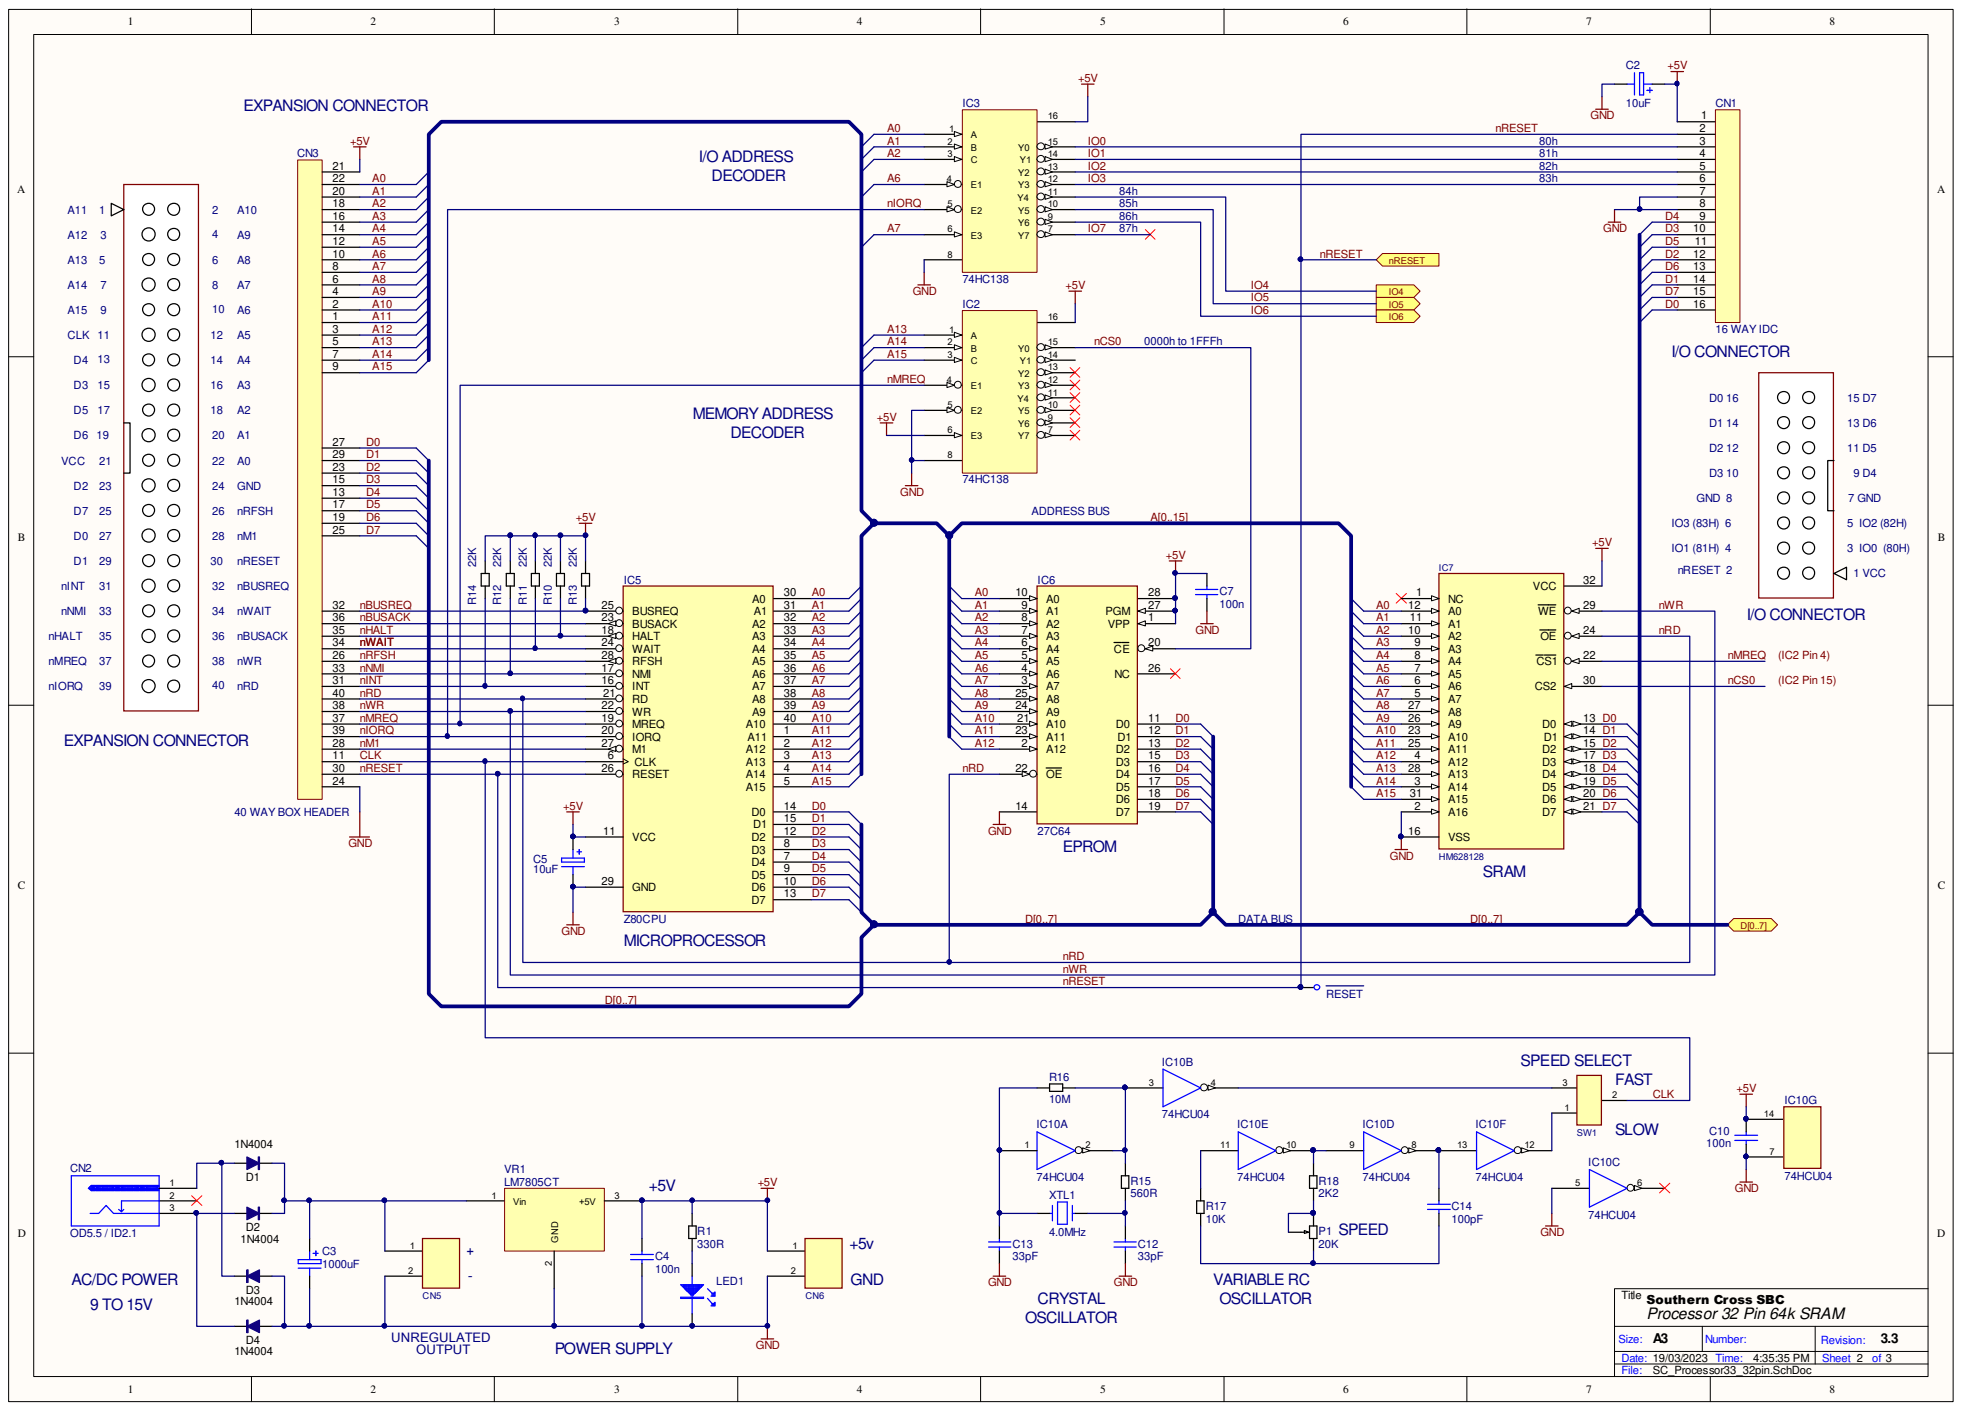
[picture p87: page 3]

# Static RAM Pinouts

512k | 128k | 32k | 8k | 2k | 2k | 8k | 32k | 128k | 512k

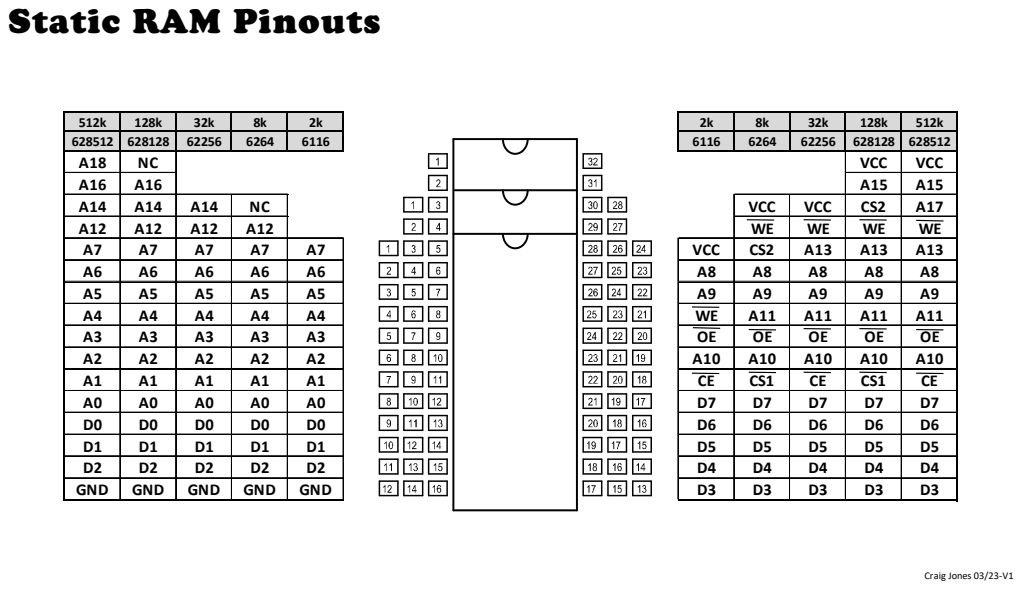
[picture p88: page 4]
