crsjones/Southern-Cross-Computer-z80/SC-BP_Backplane/SC-BP-02/SC-BP-01_Schematic.pdf

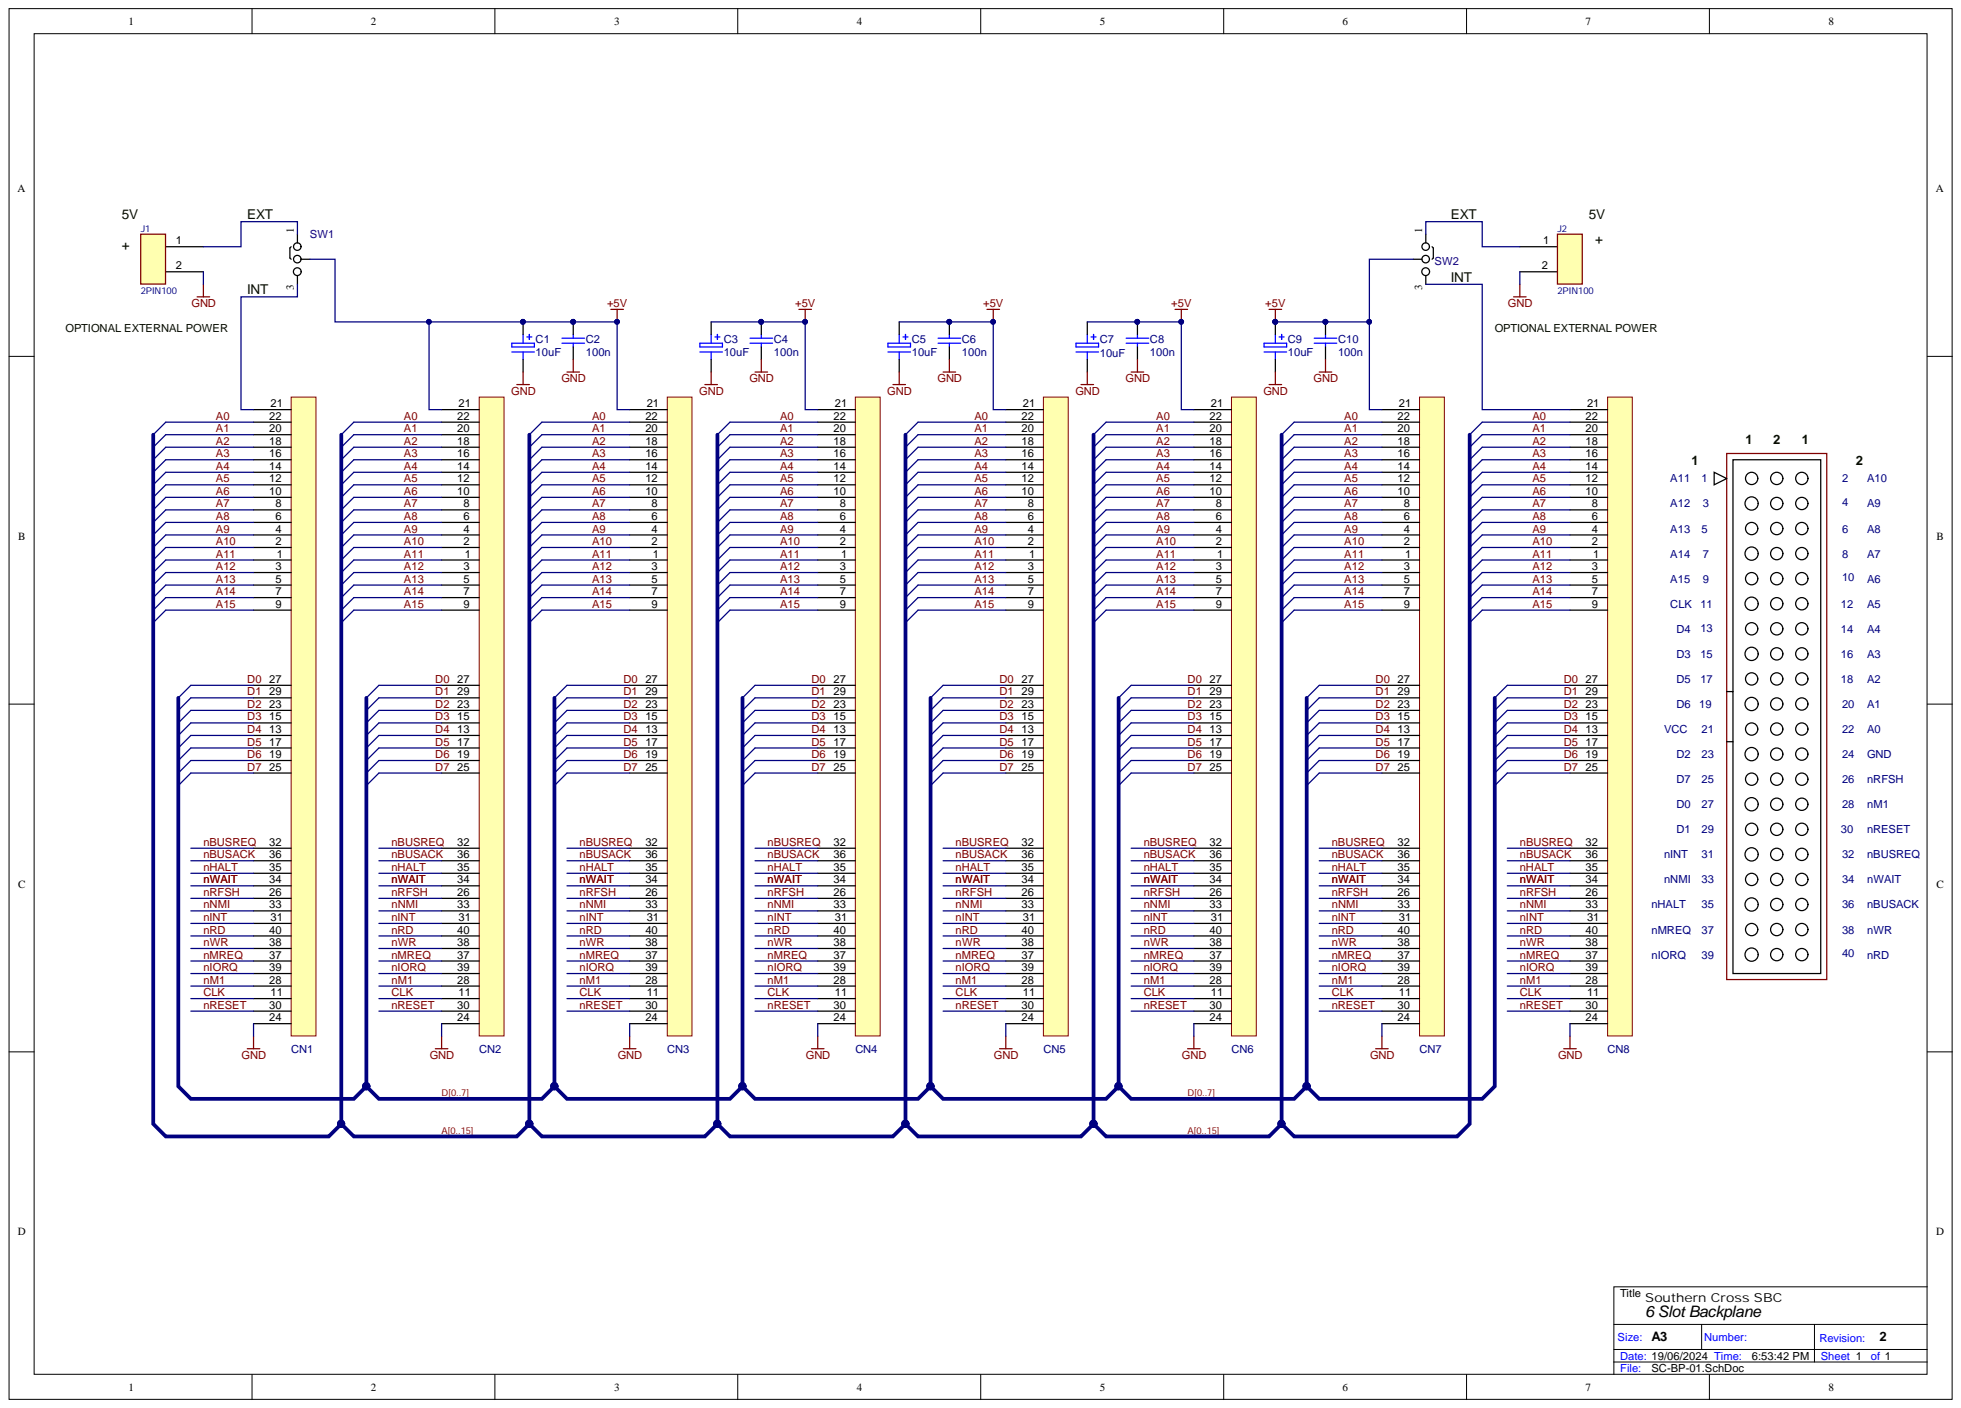
[picture p91: page 1]

Size: A3 | Number: | Revision: 2
Date: 19/06/2024 Time: 6:53:42 PM | | Sheet 1 of 1
