crsjones/Southern-Cross-Computer-z80/SC-6850_Serial/SC-Serial_R2/SC-Serial_V3_Schematic.pdf

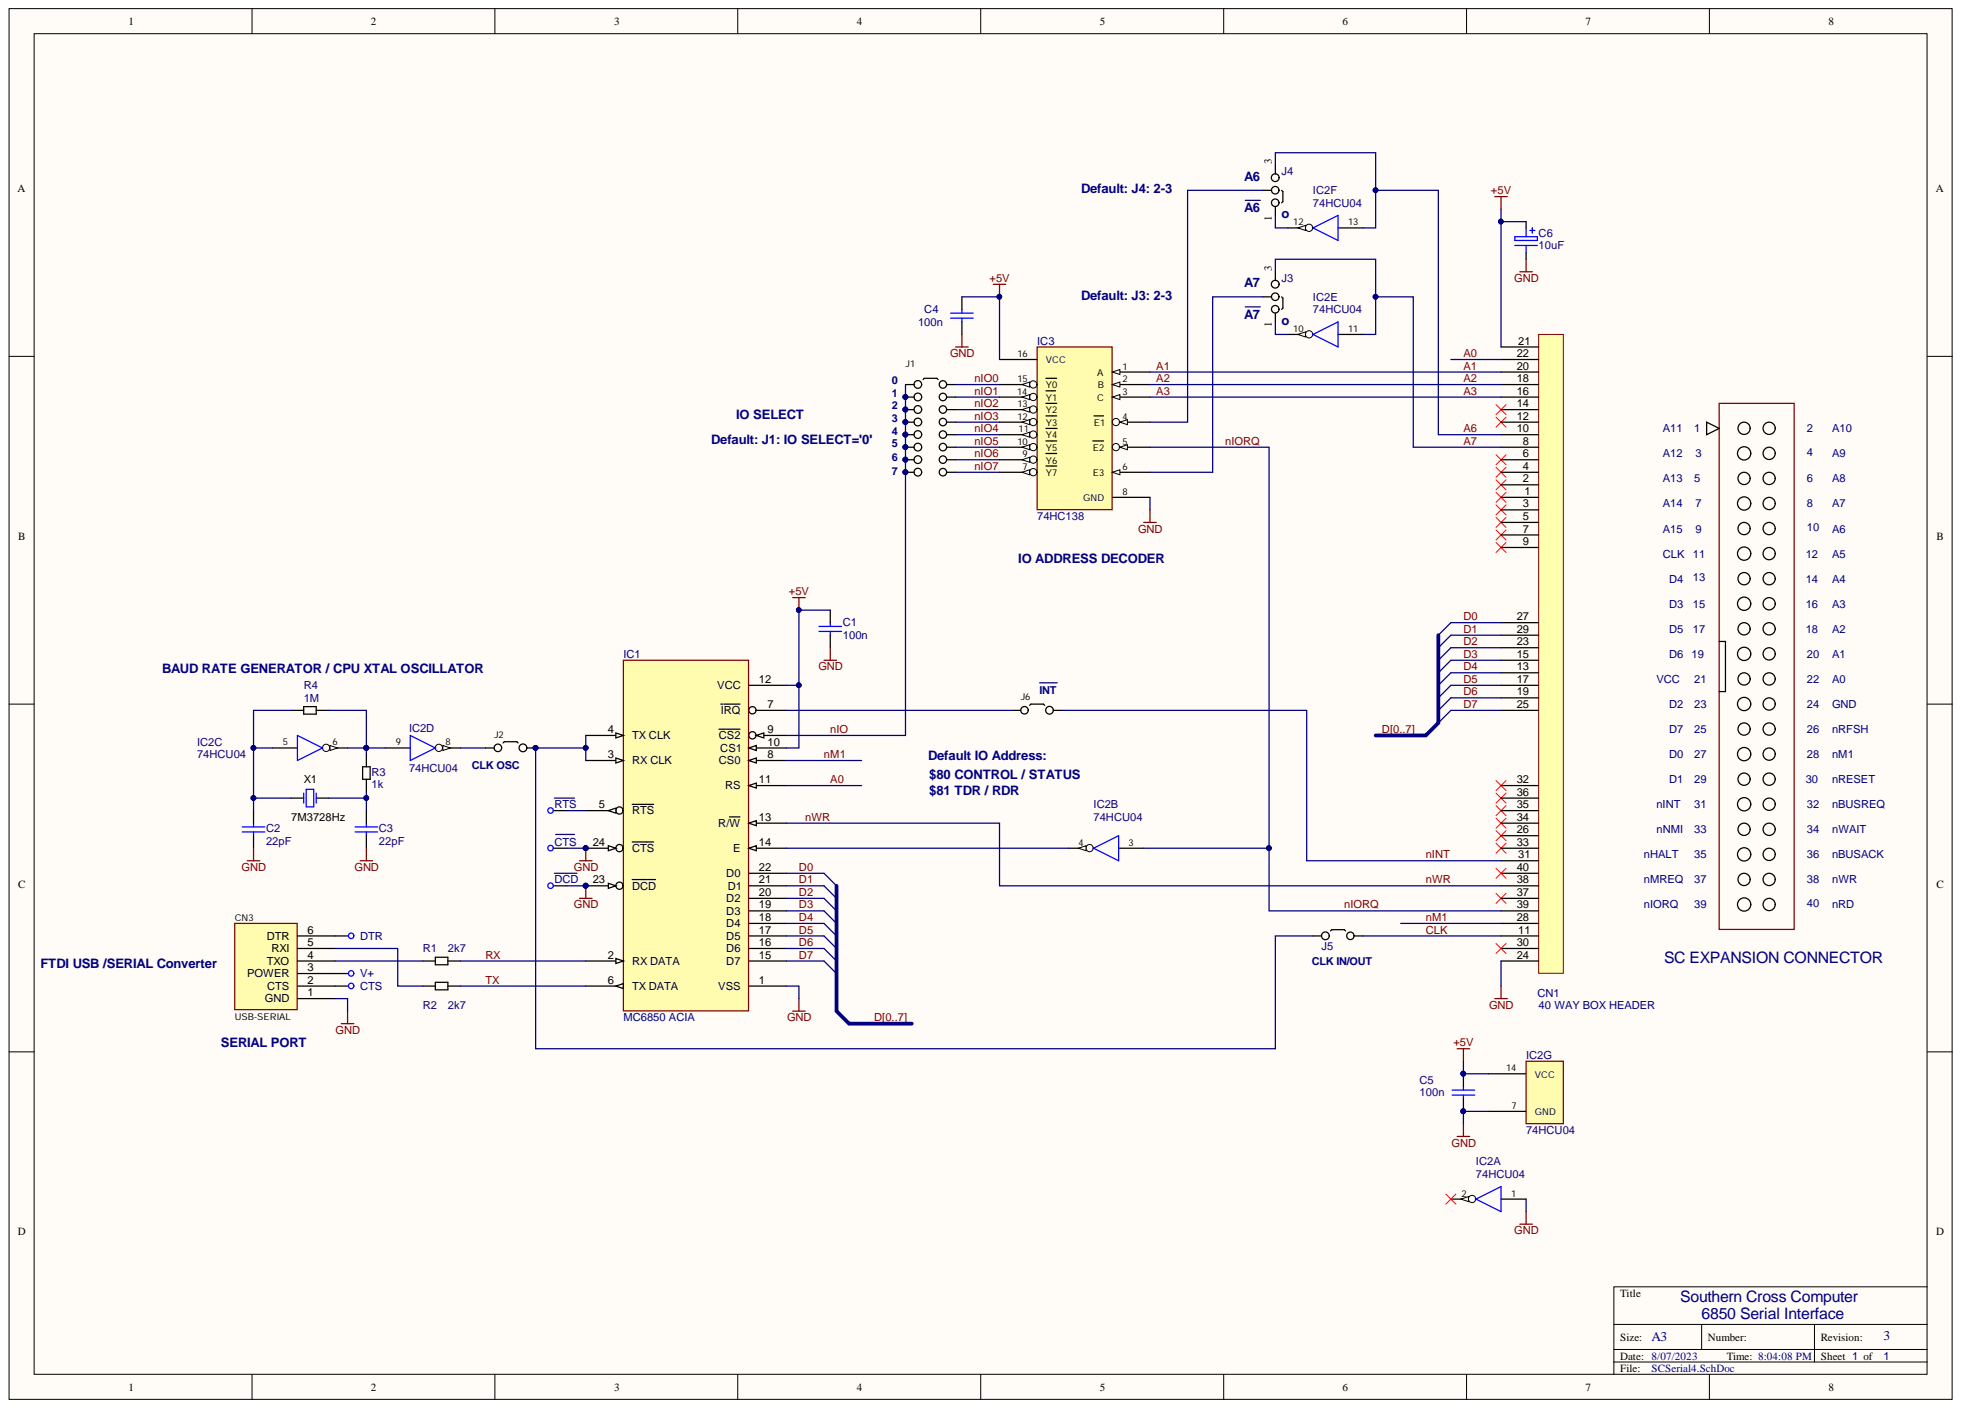
[picture p92: page 1]

BAUD RATE GENERATOR / CPU XTAL OSCILLATOR

FTDI USB /SERIAL Converter

Size: A3 | Number: | Revision: 3

Date: 8/07/2023 Time: 8:04:08 PM | | Sheet 1 of 1
