crsjones/Southern-Cross-Computer-z80/SC-APU/SC-APU-R2/SC-APU-R3_Schematic.pdf

## V C C

2 0

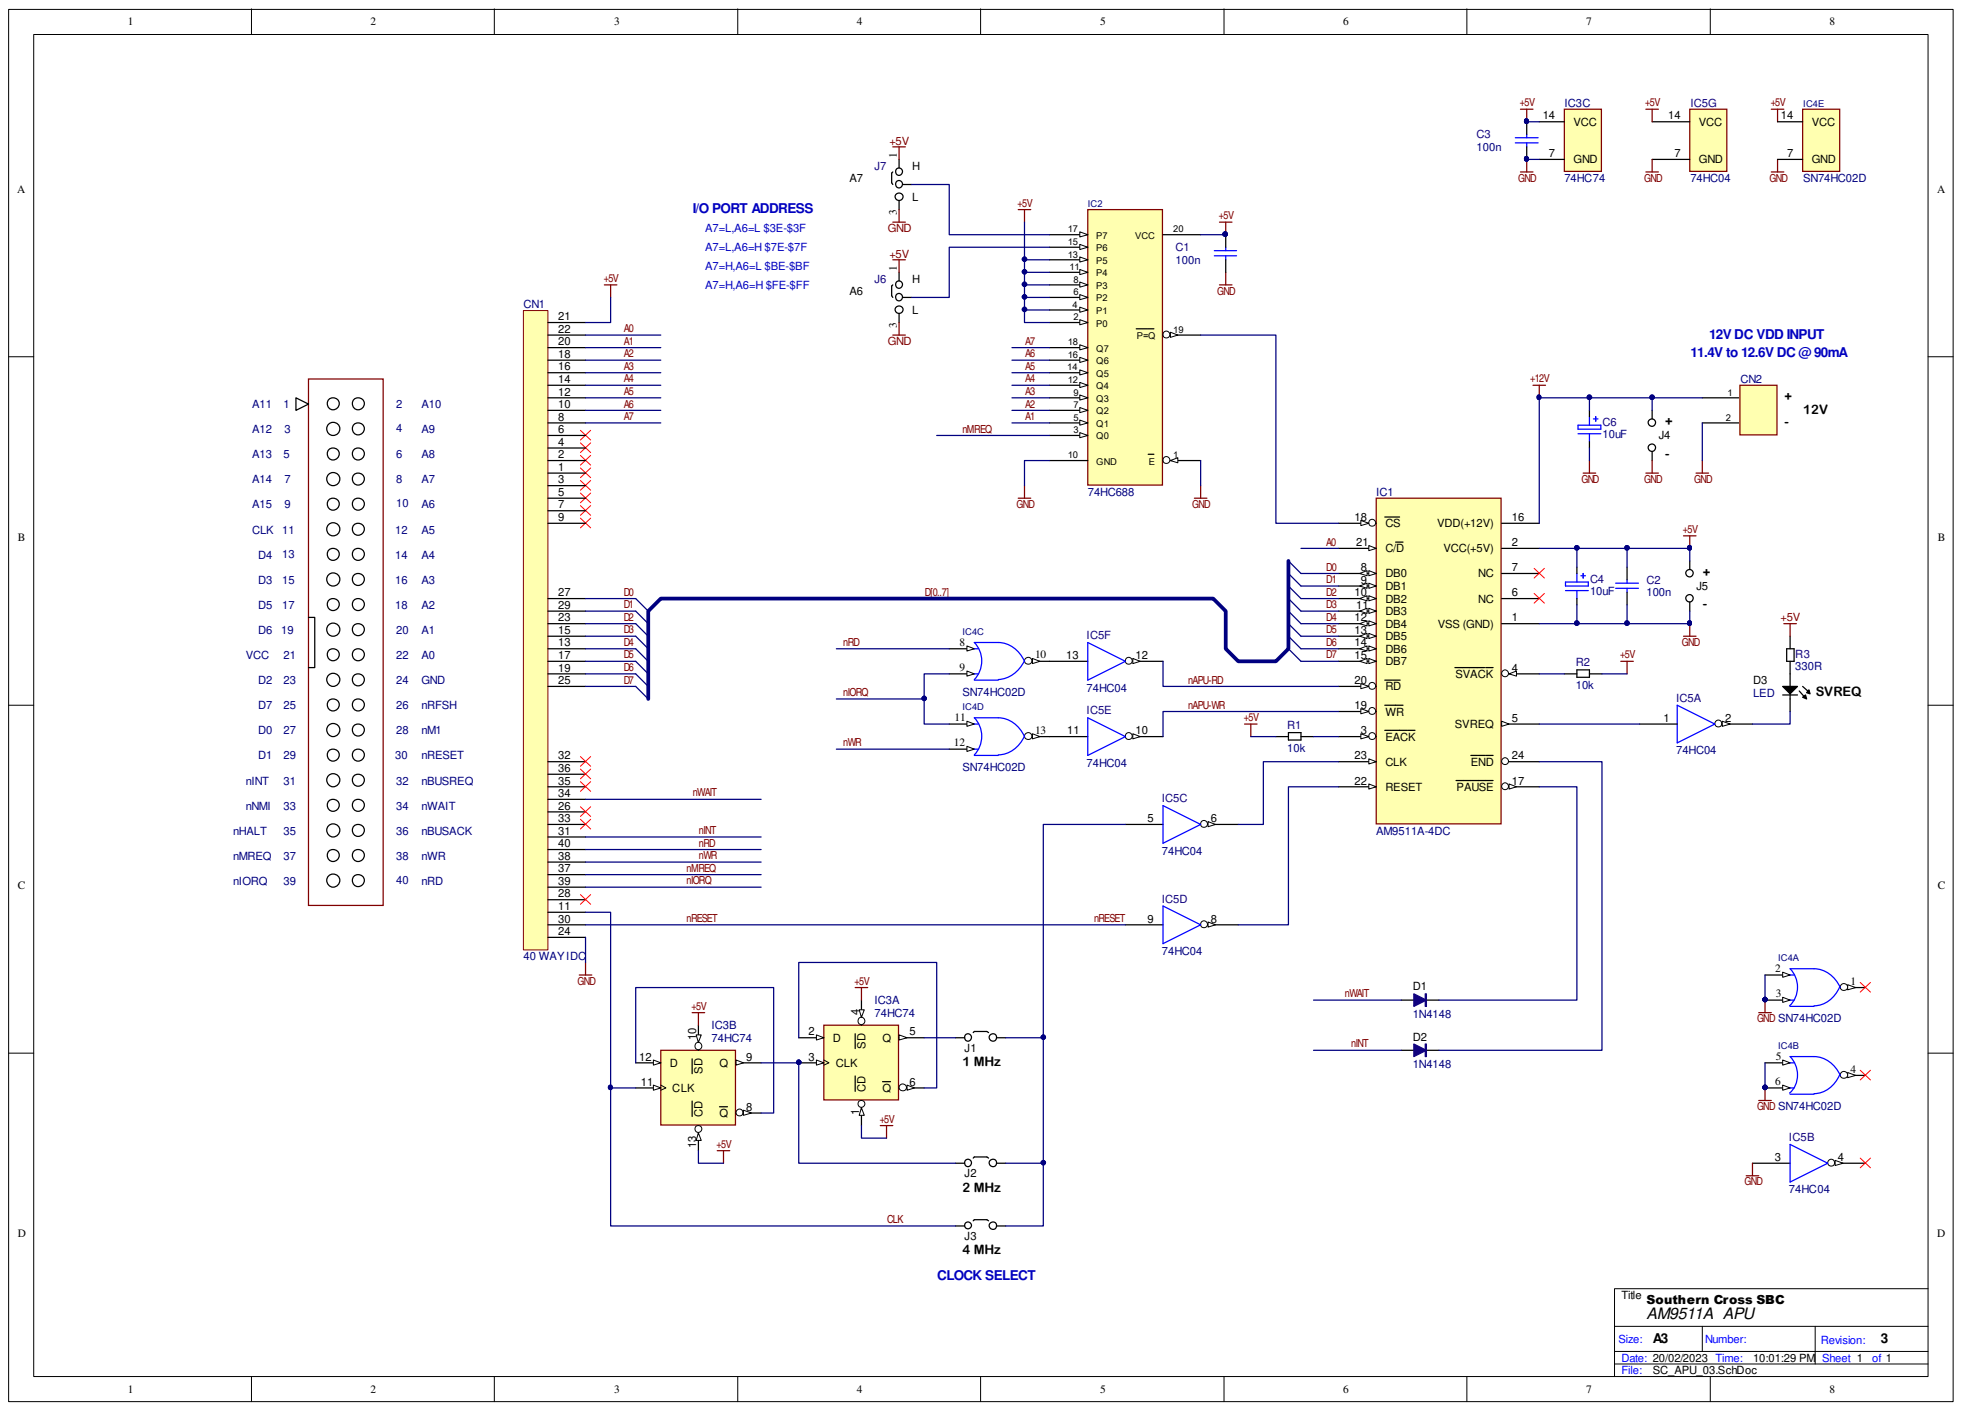
[picture p93: page 1]
