crsjones/Southern-Cross-Computer-z80/SC-6850_Serial/SC-Serial_R1/SC-Serial_R1_ComponentOverlay.pdf

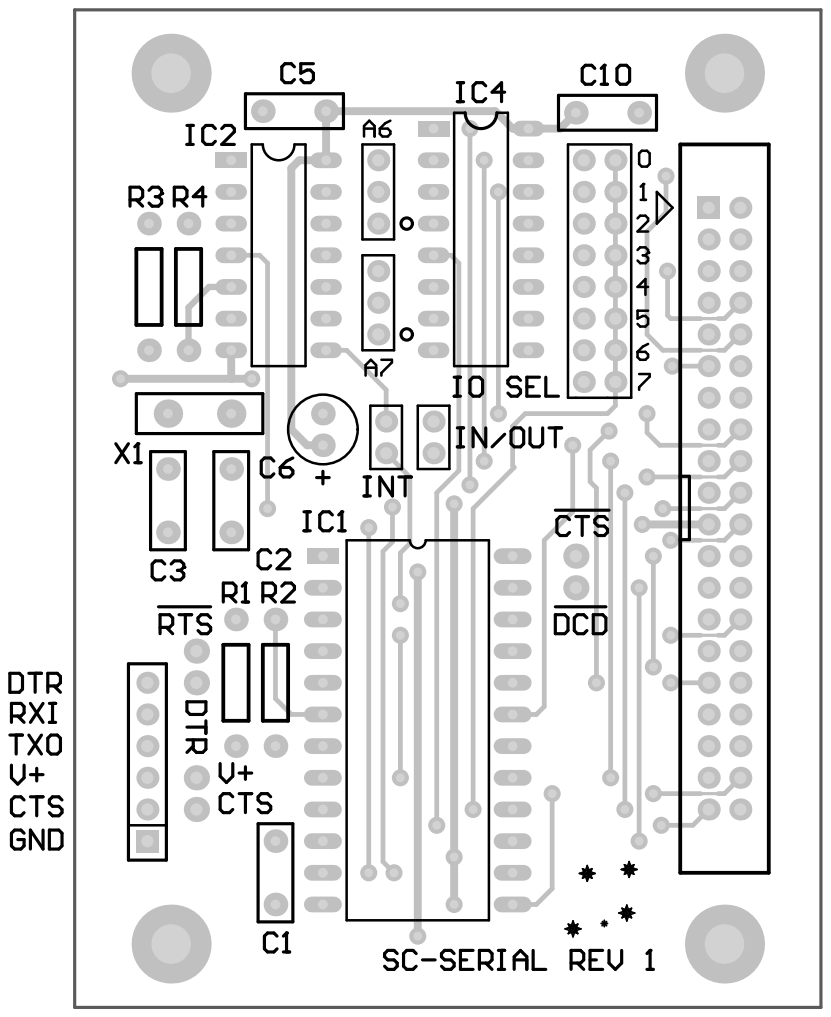
[picture p94: page 1]
