crsjones/Southern-Cross-Computer-z80/SC-6850_Serial/SC-Serial_R1/SC-Serial_R1_Schematic.pdf

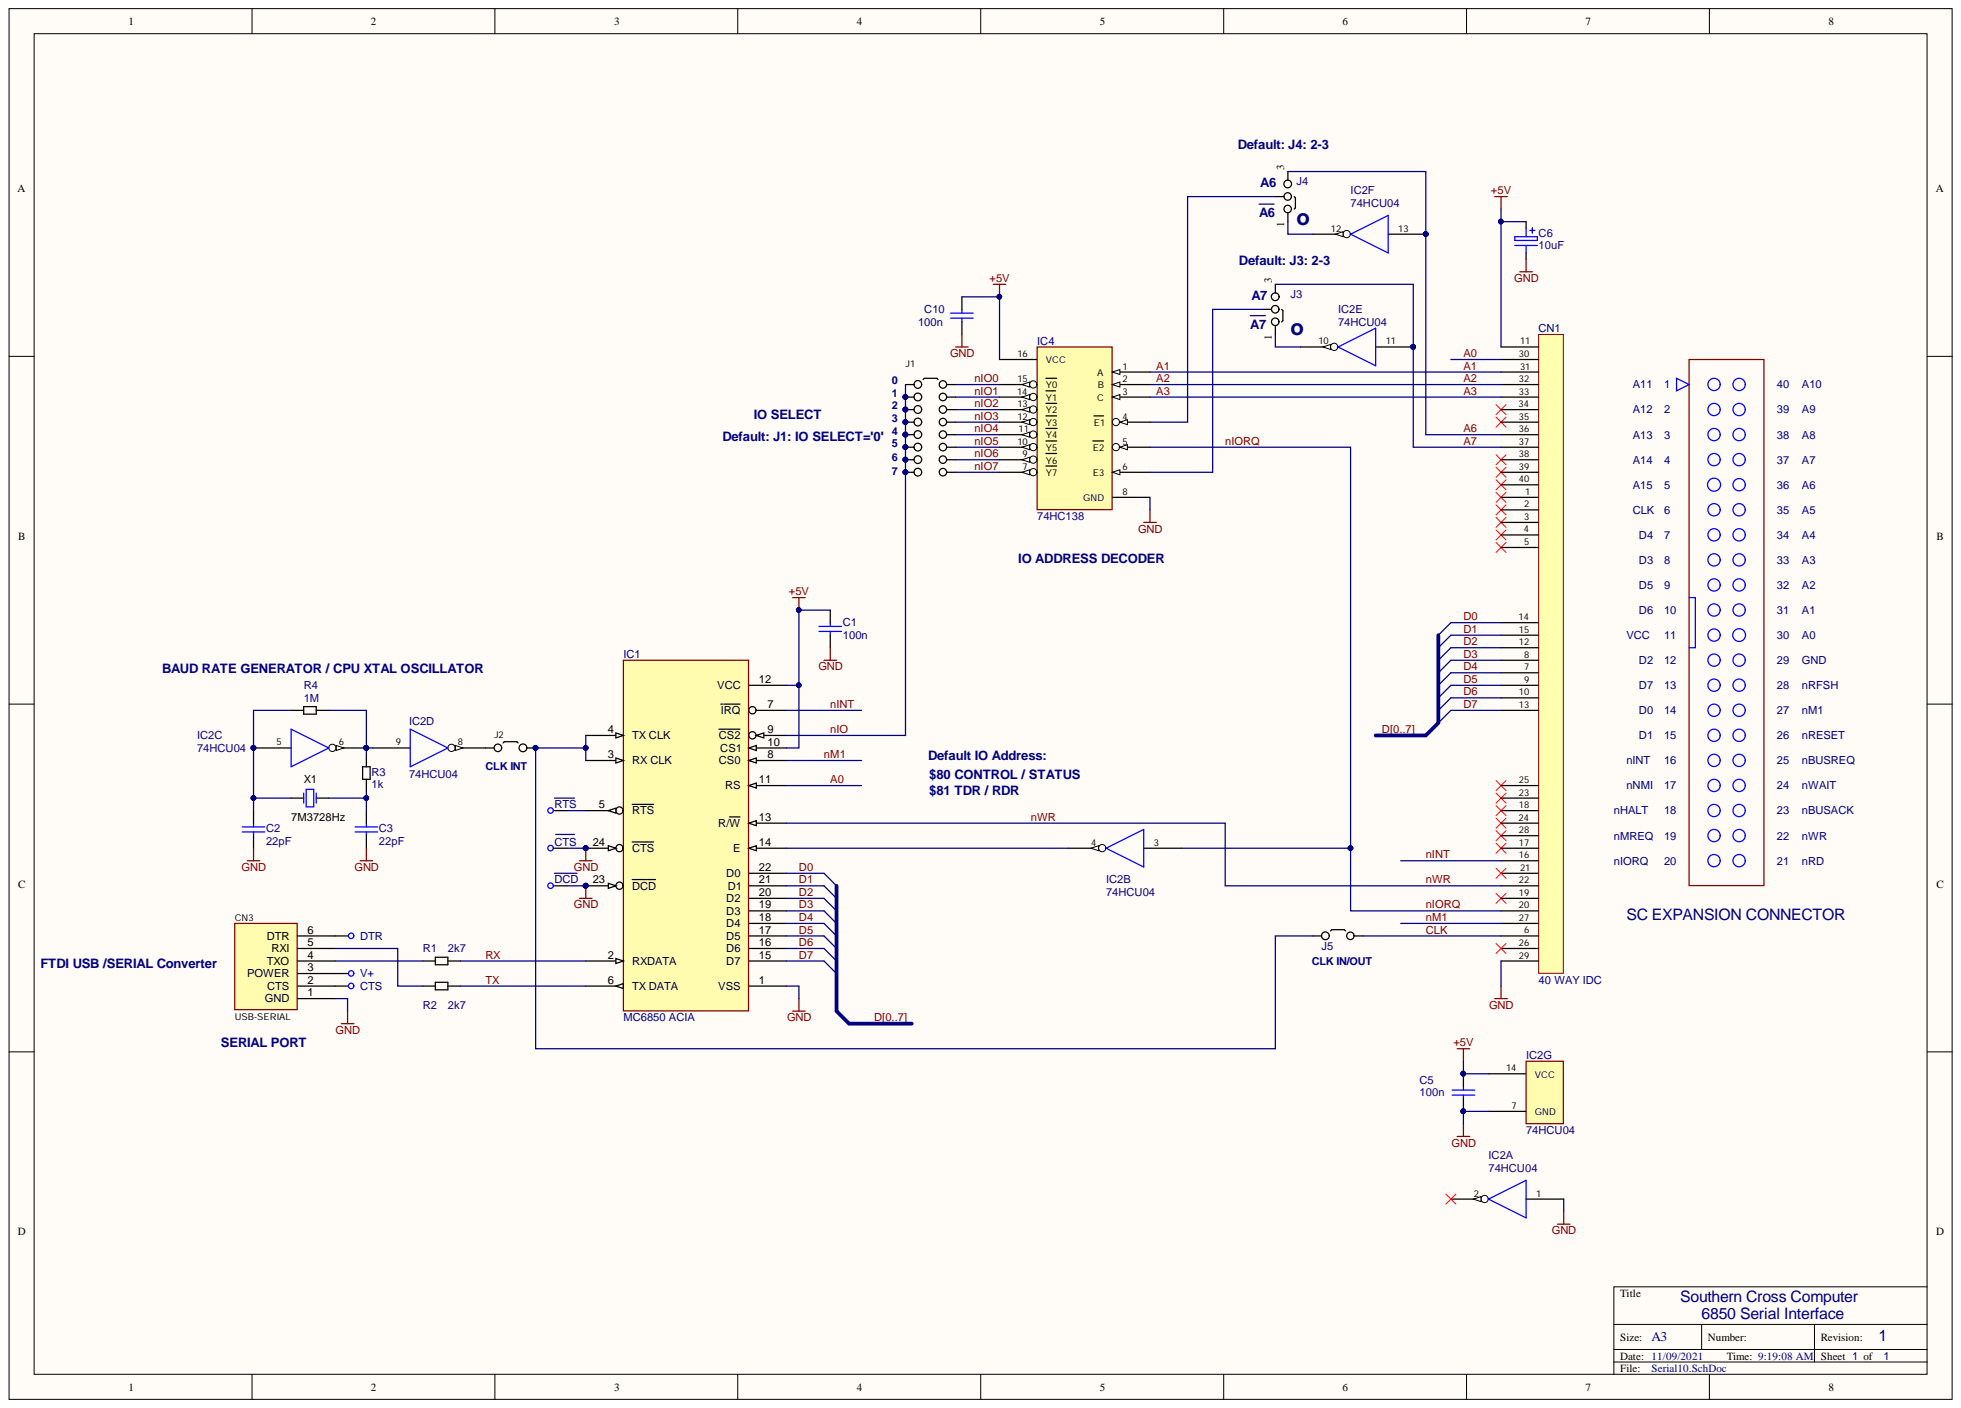
[picture p95: page 1]

BAUD RATE GENERATOR / CPU XTAL OSCILLATOR

FTDI USB /SERIAL Converter

Size: A3 | Number: | Revision: 1

Date: 11/09/2021 Time: 9:19:08 AM | | Sheet 1 of 1
