crsjones/Southern-Cross-Computer-z80/SC-CF/SC-CFA-02.pdf

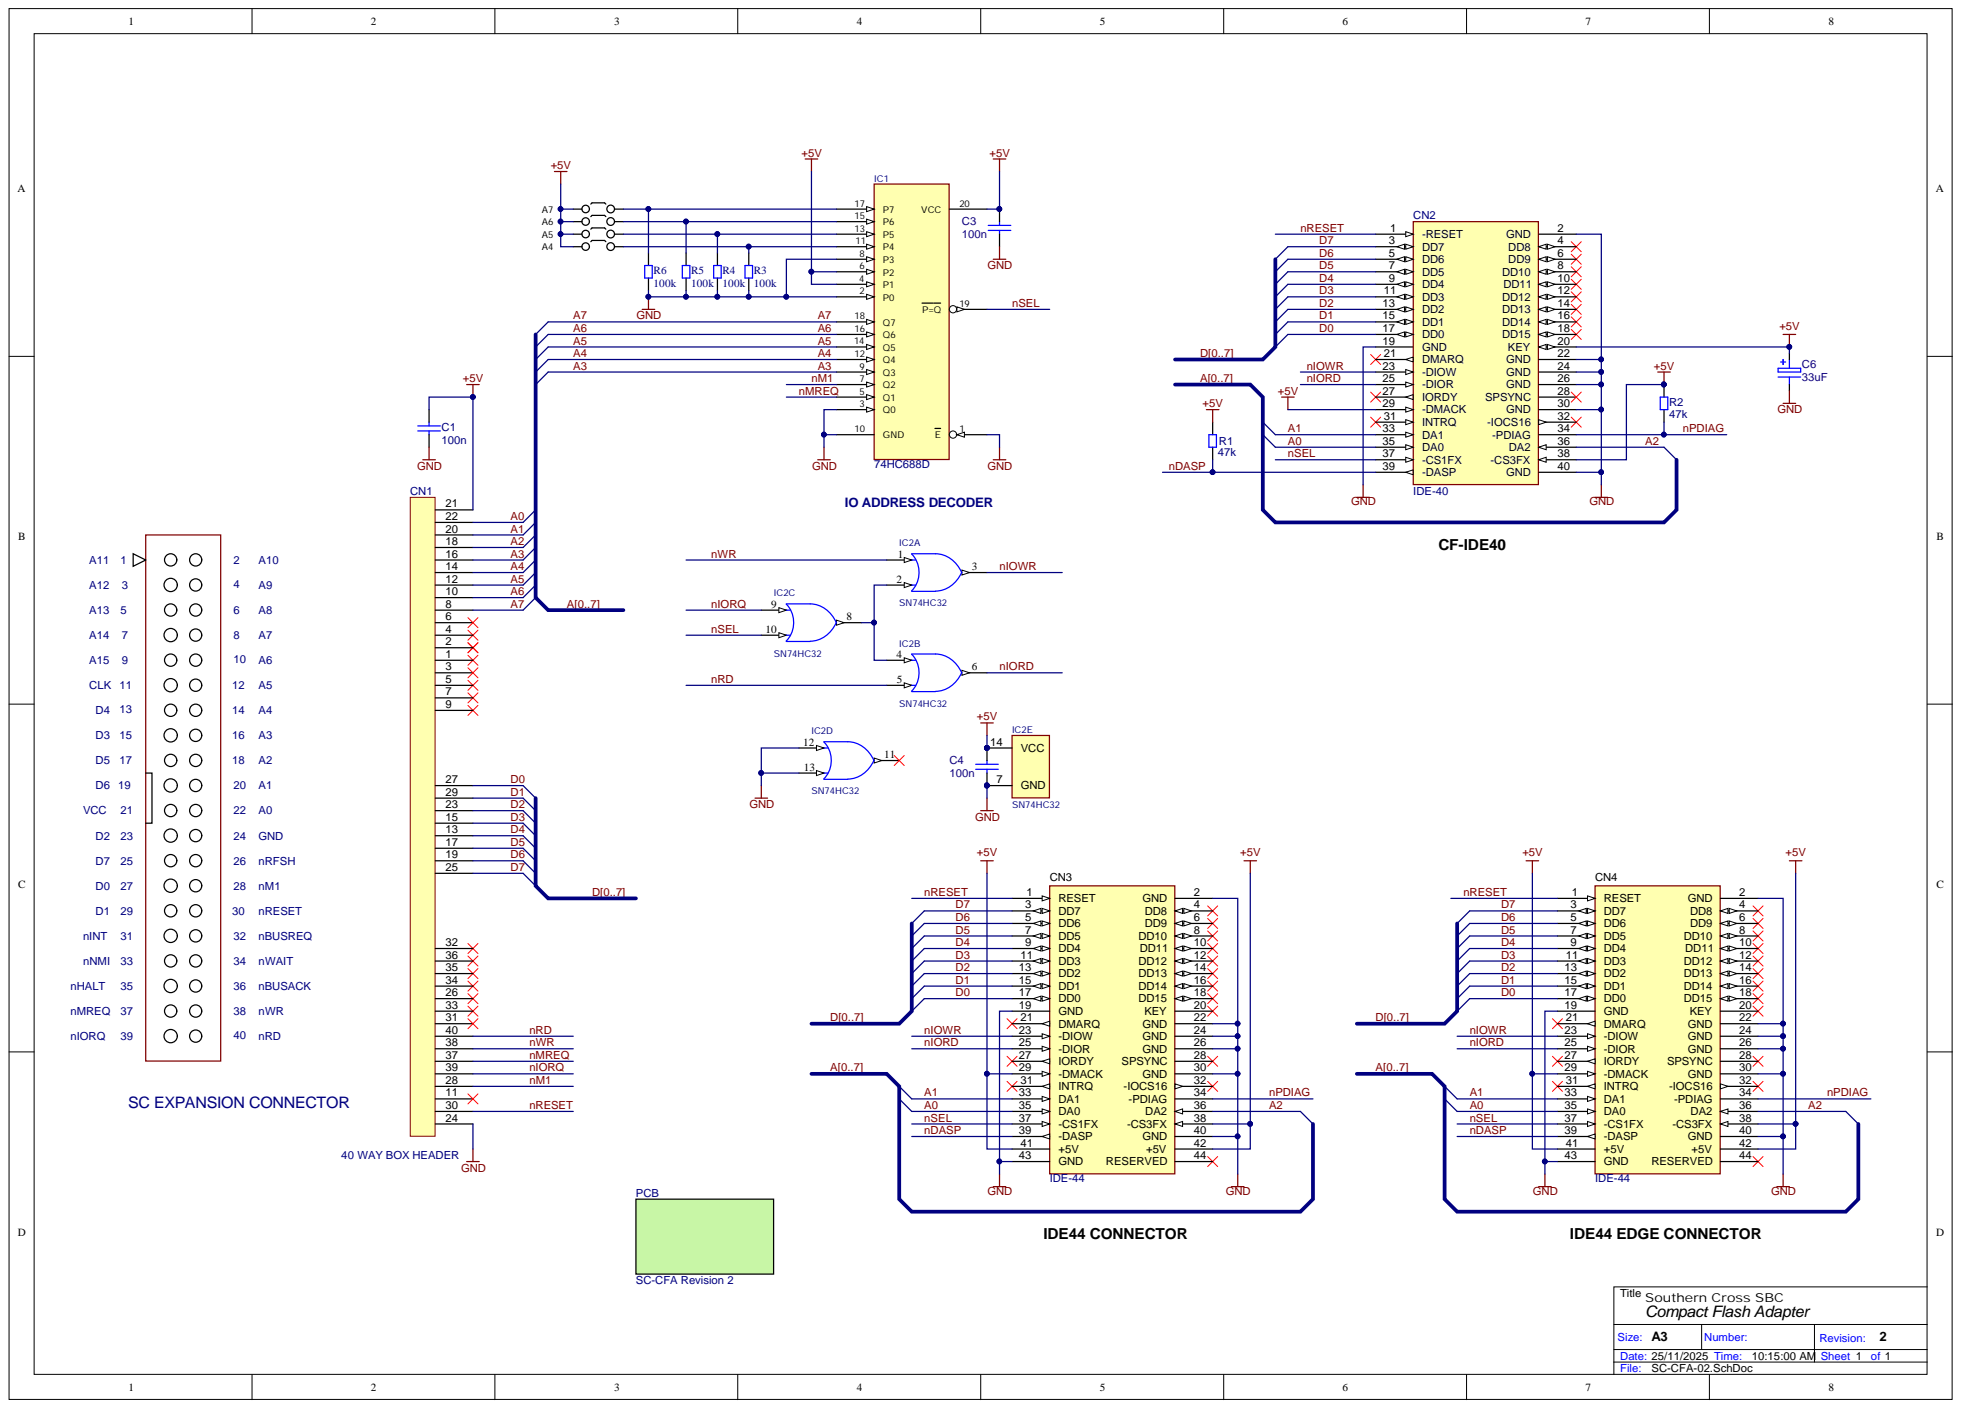
[picture p96: page 1]

Size: A3 | Number: | Revision: 2
Date: 25/11/2025 Time: 10:15:00 AM | | Sheet 1 of 1
