crsjones/Southern-Cross-Computer-z80/SC-GBCART/SC-GBCart02.pdf

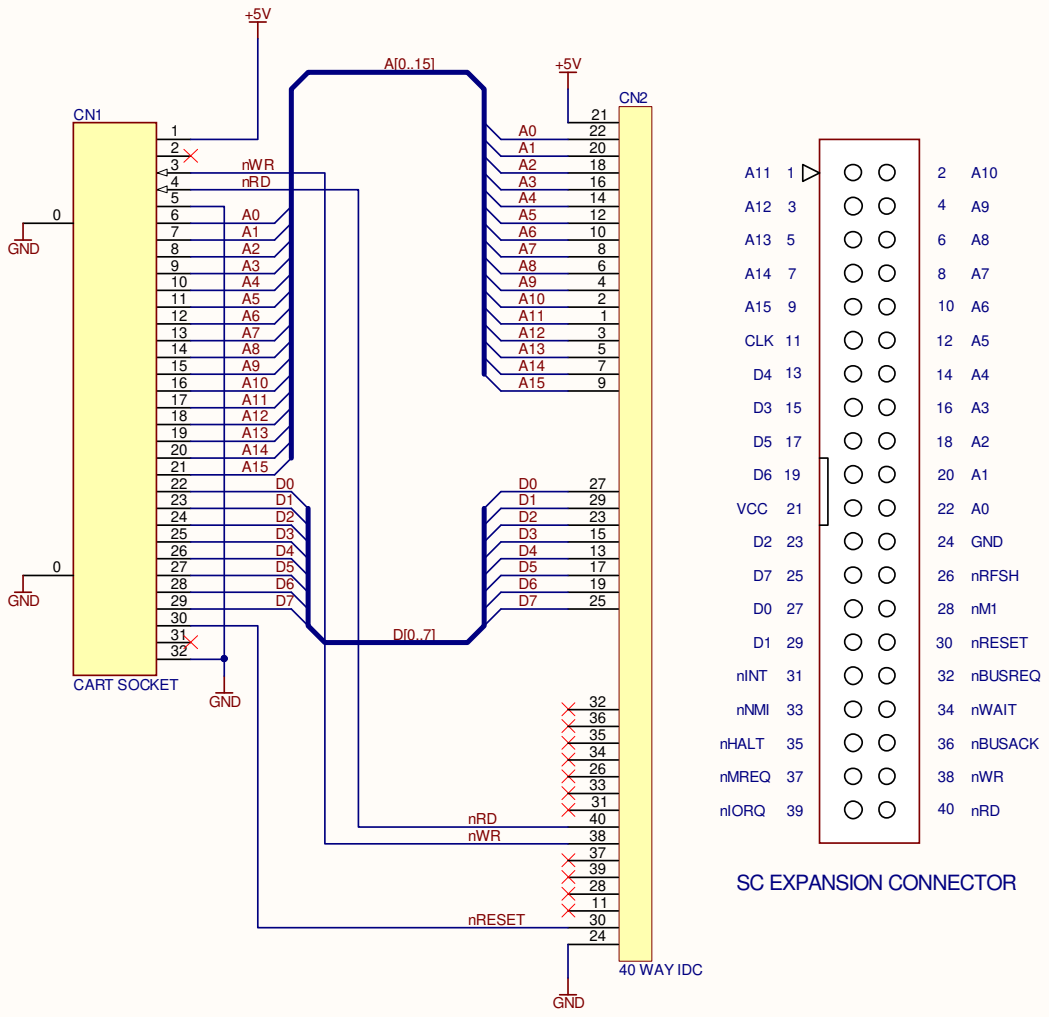
[picture p97: page 1]
