crsjones/Southern-Cross-Computer-z80/SC-APU/SC-APU-R1/SC-APU-R1.pdf

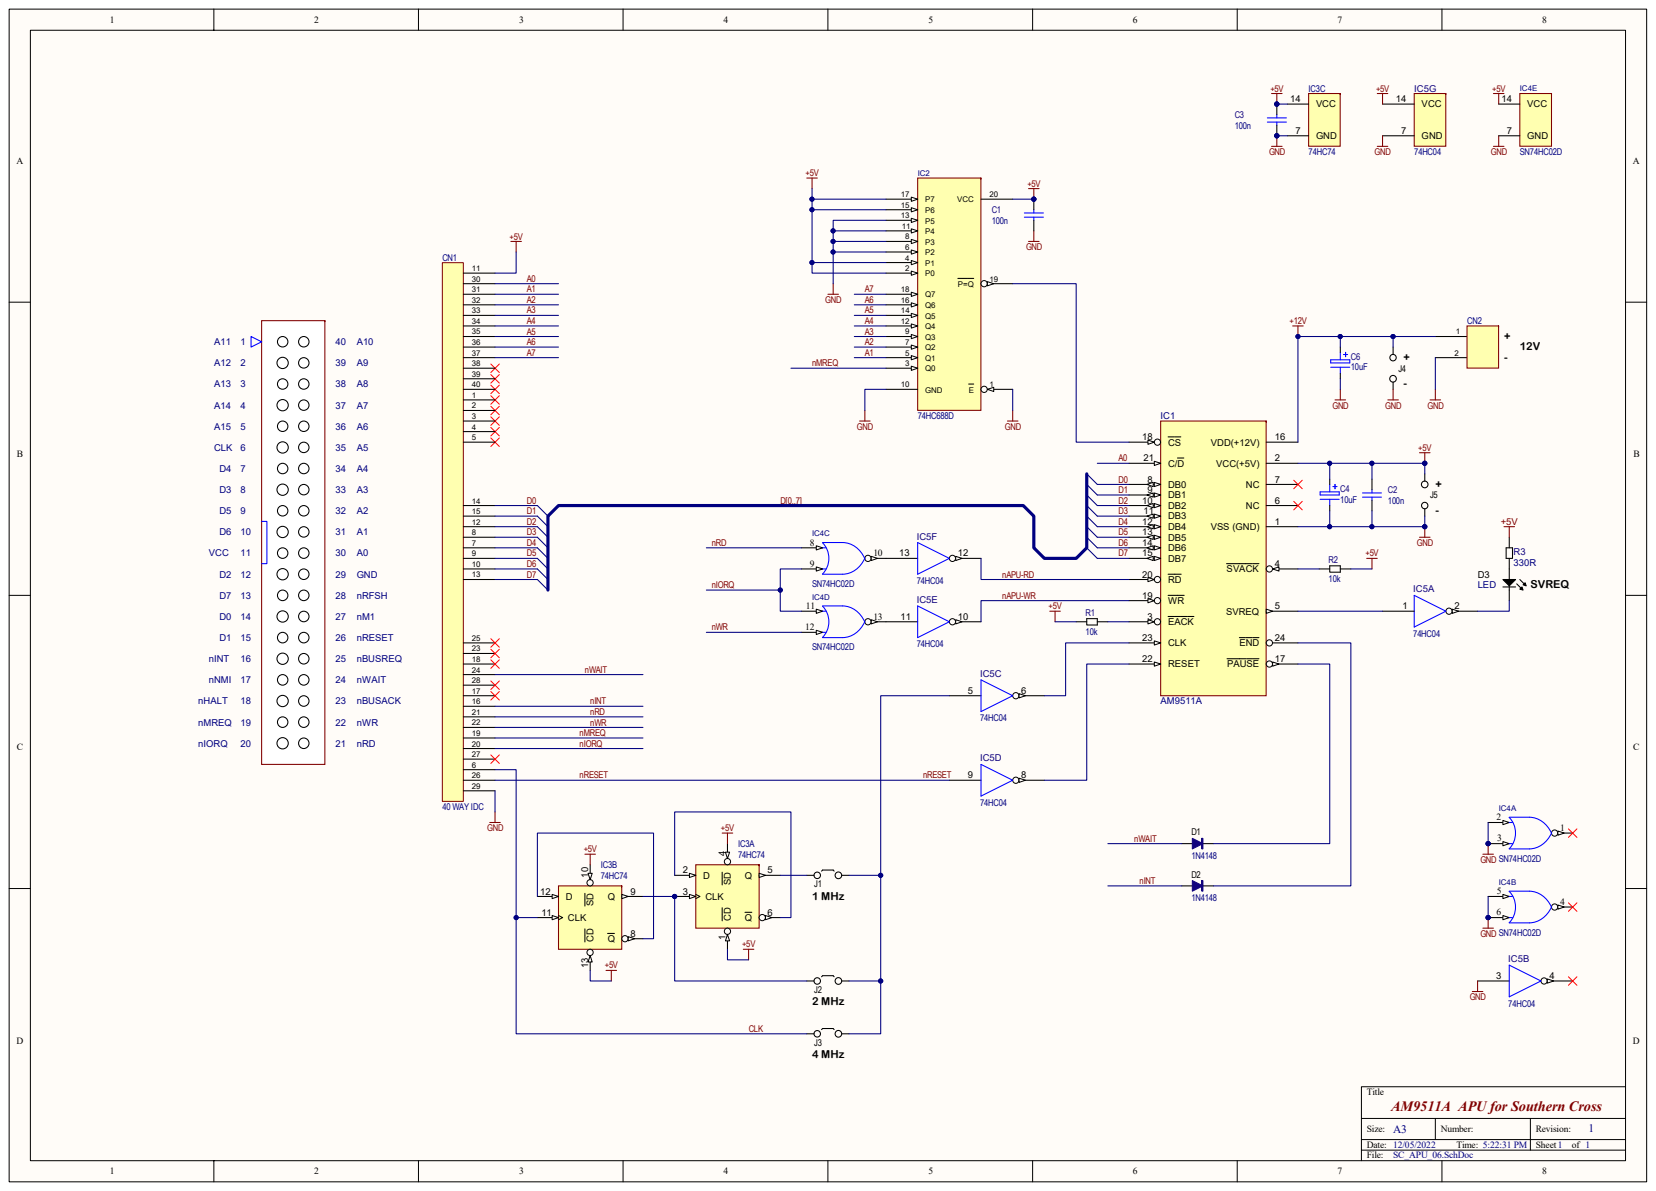
[picture p98: page 1]
