crsjones/Southern-Cross-Computer-z80/SC-APU/SC-APU-R1/SC-APU-R1_Overlay.pdf

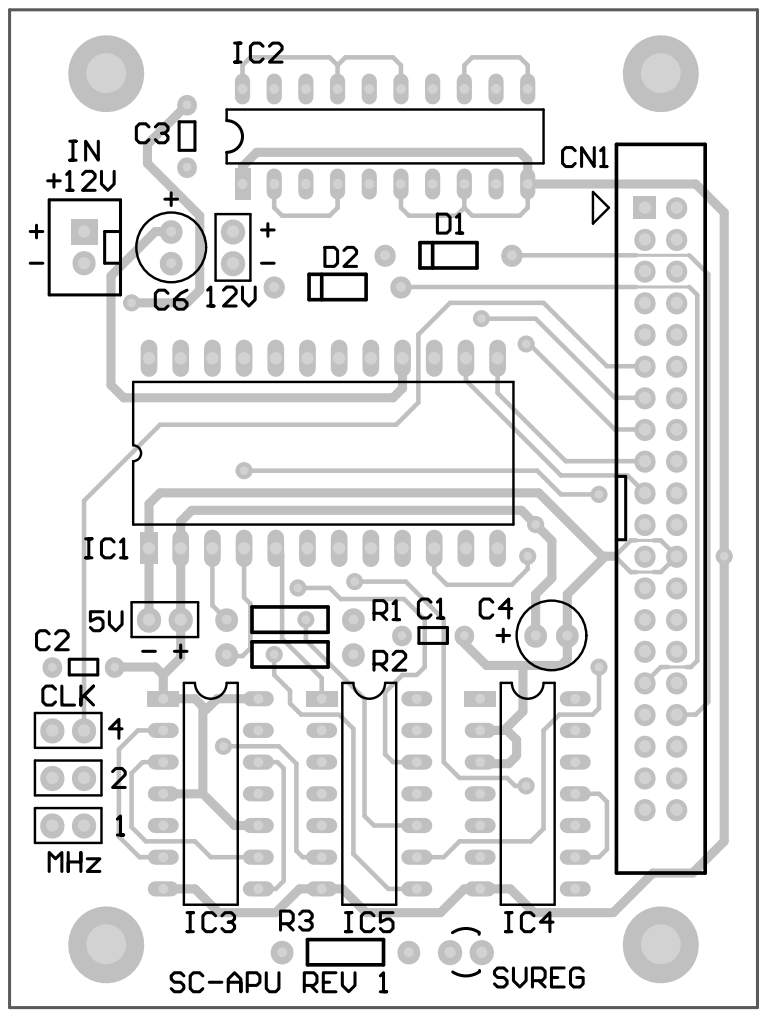
[picture p99: page 1]
